OpenScan-org/OpenScan-Design/images/black-shield-config.png

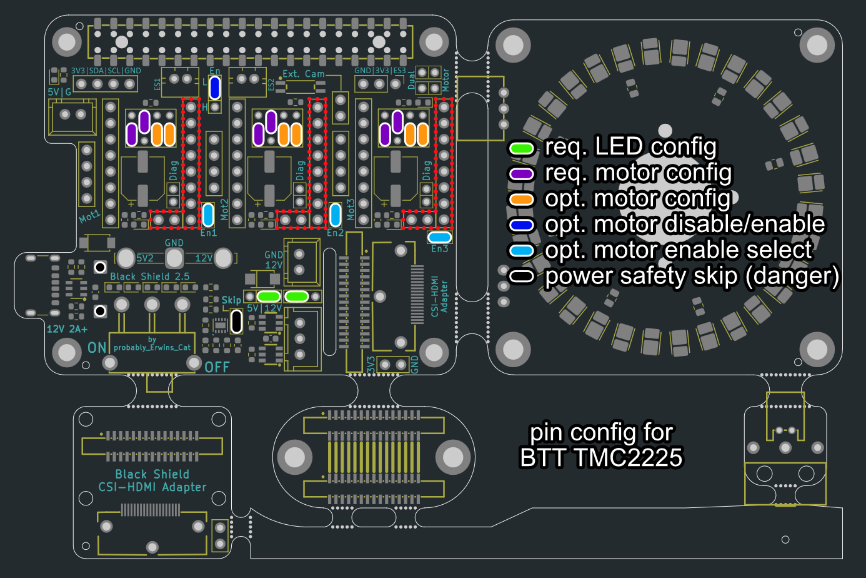
images/black-shield-config.png
