OpenScan-org/OpenScan-Design/images/cog-wheel-height-rotor.png

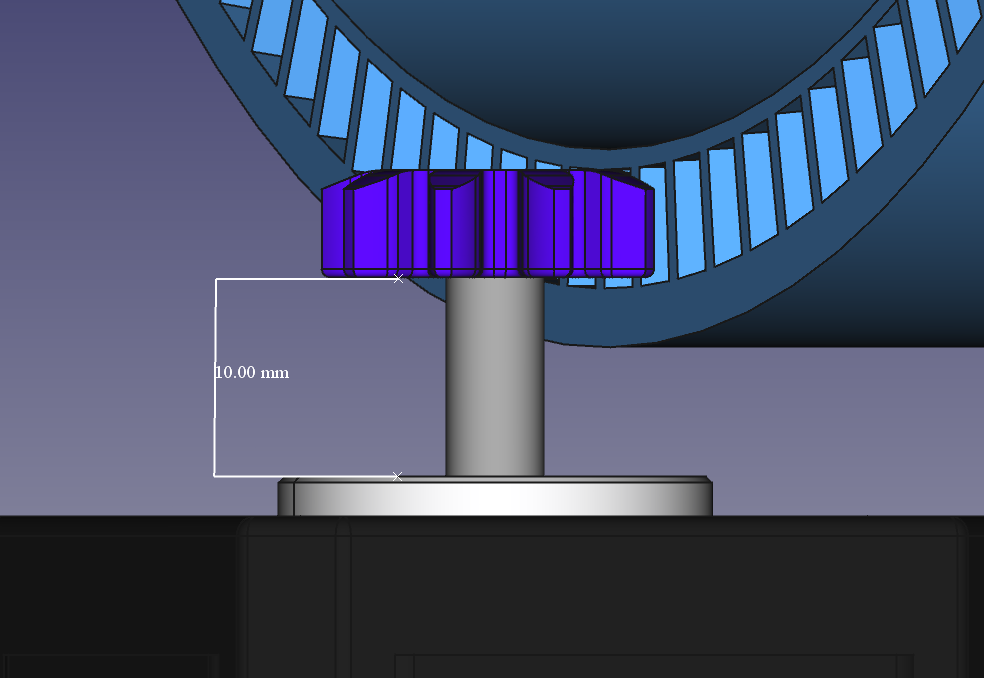
images/cog-wheel-height-rotor.png
