OpenScan-org/OpenScan-Design/images/OpenScanMiniV2Beta.jpg

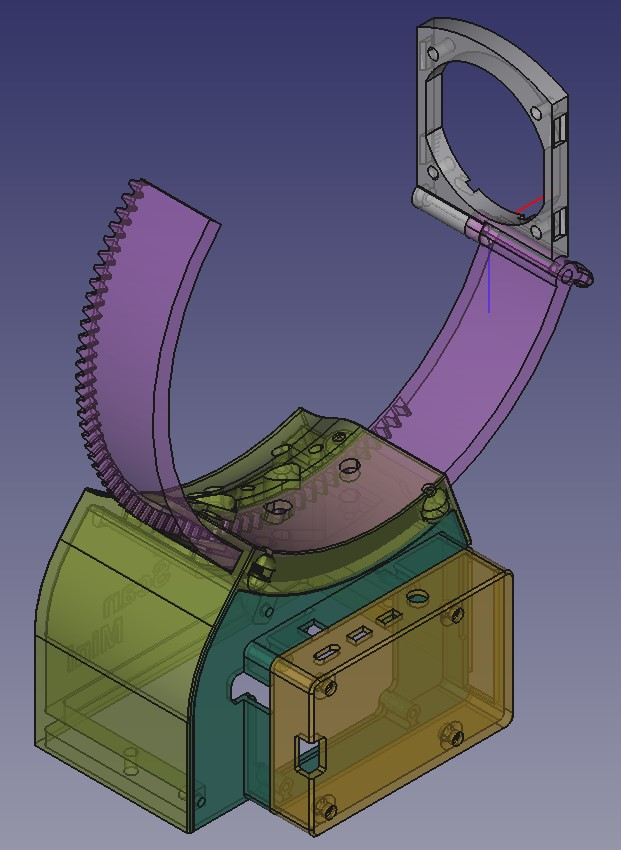
images/OpenScanMiniV2Beta.jpg
