OpenScan-org/OpenScan-Design/usermods/Turntables for D-shaped Shafts/80mm Stand for 5cm objects.3mf

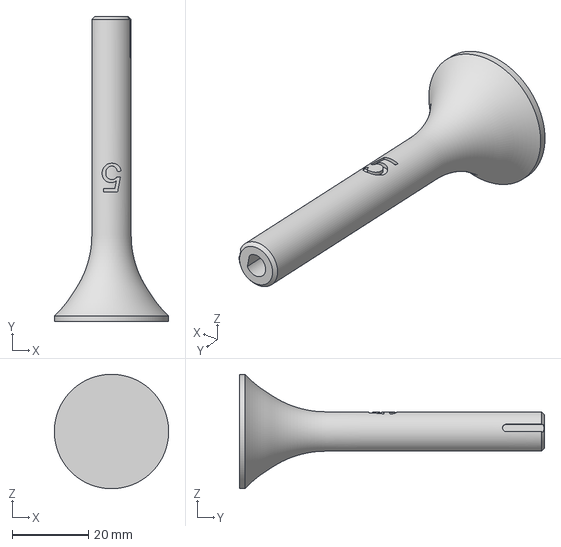
[picture p46: CAD file, 2022-10-08]
usermods/Turntables for D-shaped Shafts/80mm Stand for 5cm objects.3mf
30.0 x 80.0 x 30.0 mm
