OpenScan-org/OpenScan-Design/files/Classic/V1/Turntable_-_Adapter_small.step

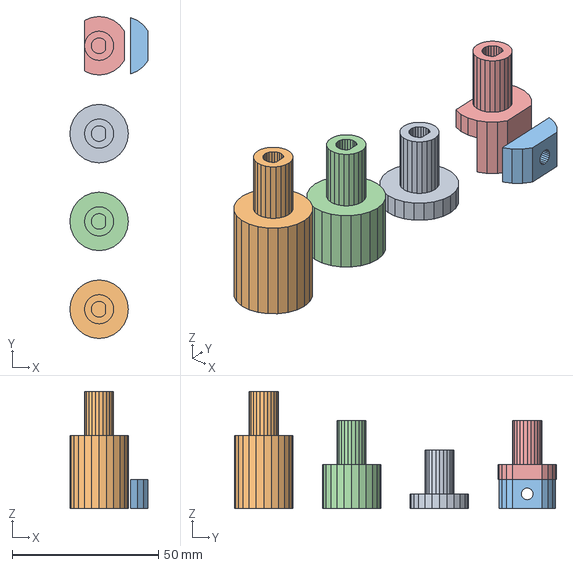
[picture p47: CAD file, 2025-07-07]
files/Classic/V1/Turntable_-_Adapter_small.step
26.8 x 110.0 x 40.0 mm
