OpenScan-org/OpenScan-Design/files/Imaging-Unit/STEP/3-IU-frame.step

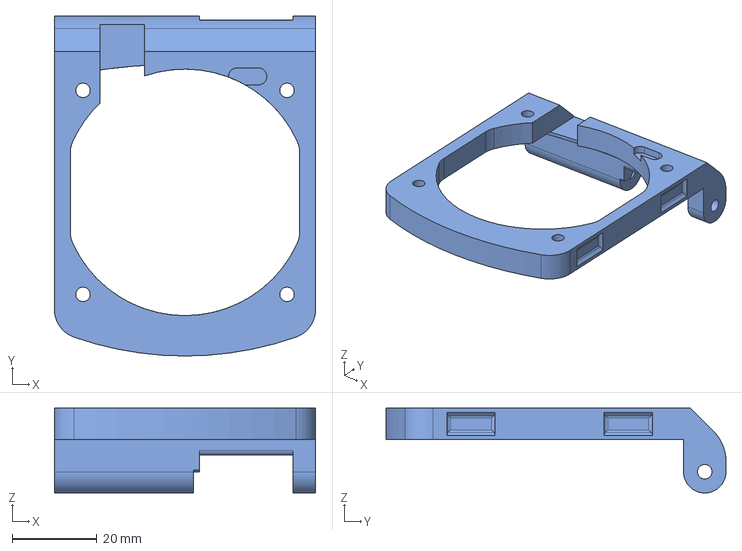
[picture p48: CAD file, 2024-12-12]
files/Imaging-Unit/STEP/3-IU-frame.step
61.5 x 80.0 x 20.0 mm
