OpenScan-org/OpenScan-Design/files/Imaging-Unit/STL/2-cam-mount-slide-in (Meshed).stl

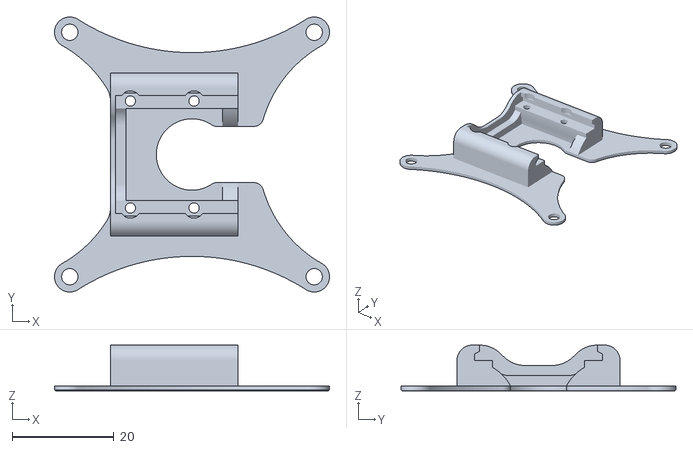
[picture p49: CAD file, 2024-12-12]
files/Imaging-Unit/STL/2-cam-mount-slide-in (Meshed).stl
54.0 x 54.0 x 9.00
