OpenScan-org/OpenScan-Design/files/Midi/V2.4/STEP/2-rotor-segmented-in-two--part-2.step

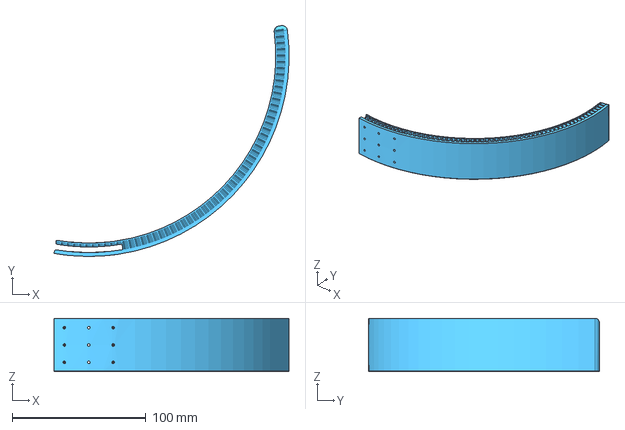
[picture p50: CAD file, 2025-06-18]
files/Midi/V2.4/STEP/2-rotor-segmented-in-two--part-2.step
176.0 x 172.9 x 40.0 mm
