OpenScan-org/OpenScan-Design/files/Midi/V2.4/STL/2-rotor-segmented-in-two--part-1 (Meshed).stl

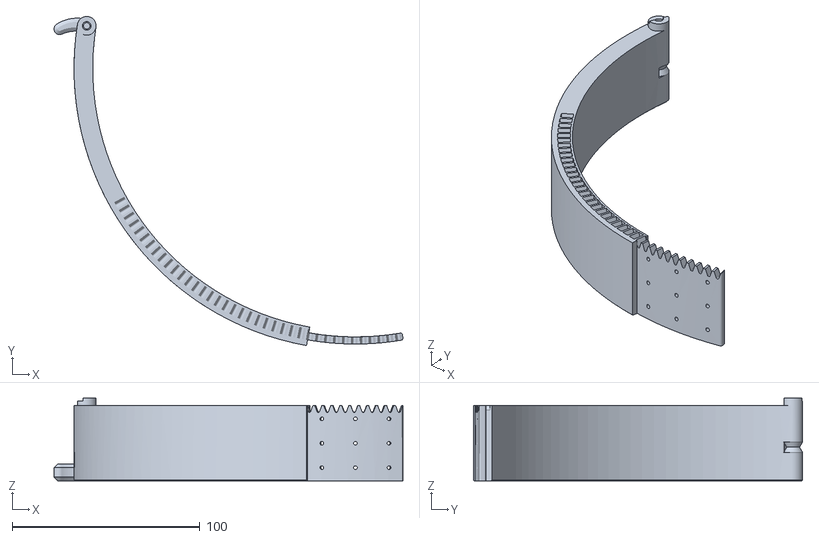
[picture p51: CAD file, 2025-06-18]
files/Midi/V2.4/STL/2-rotor-segmented-in-two--part-1 (Meshed).stl
186.0 x 175.4 x 44.0
