OpenScan-org/OpenScan-Design/files/Mini/V2.4/STEP/2-rotor-segmented-in-two--part-2.step

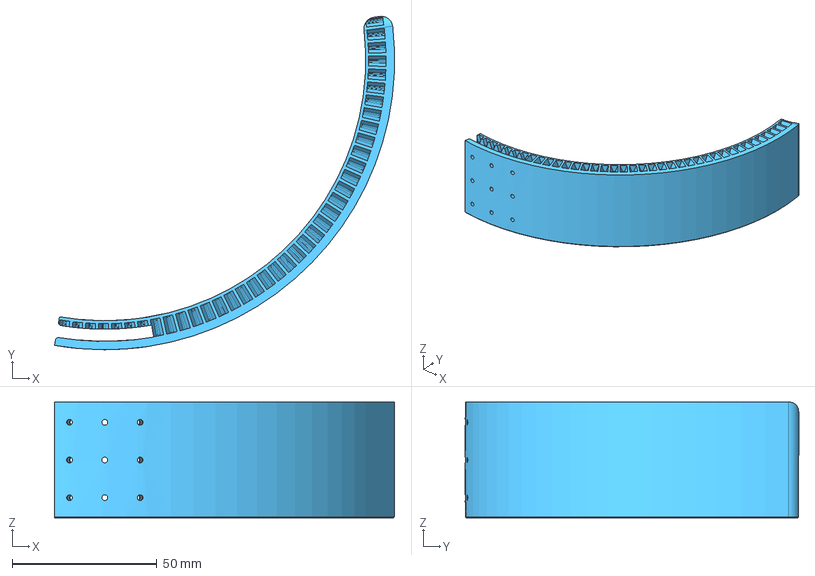
[picture p52: CAD file, 2025-06-18]
files/Mini/V2.4/STEP/2-rotor-segmented-in-two--part-2.step
117.3 x 115.1 x 40.0 mm
