OpenScan-org/OpenScan-Design/files/Mini/V2.4/STL/5-base-cover--black-shield (Meshed).stl

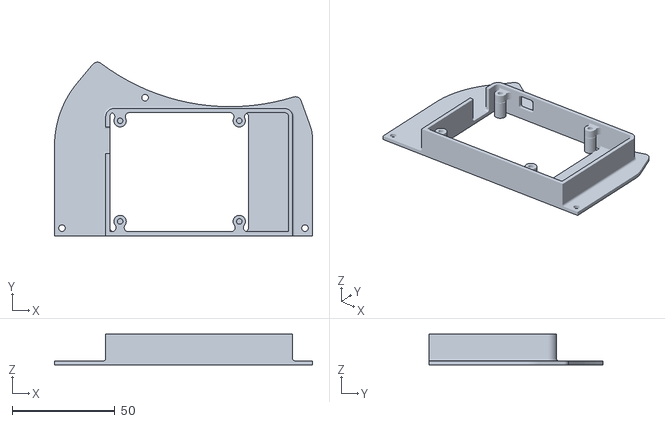
[picture p53: CAD file, 2025-06-18]
files/Mini/V2.4/STL/5-base-cover--black-shield (Meshed).stl
125.6 x 84.5 x 15.0
