OpenScan-org/OpenScan-Design/files/turntables/Midi/STEP/Turntable-90mm-object.step

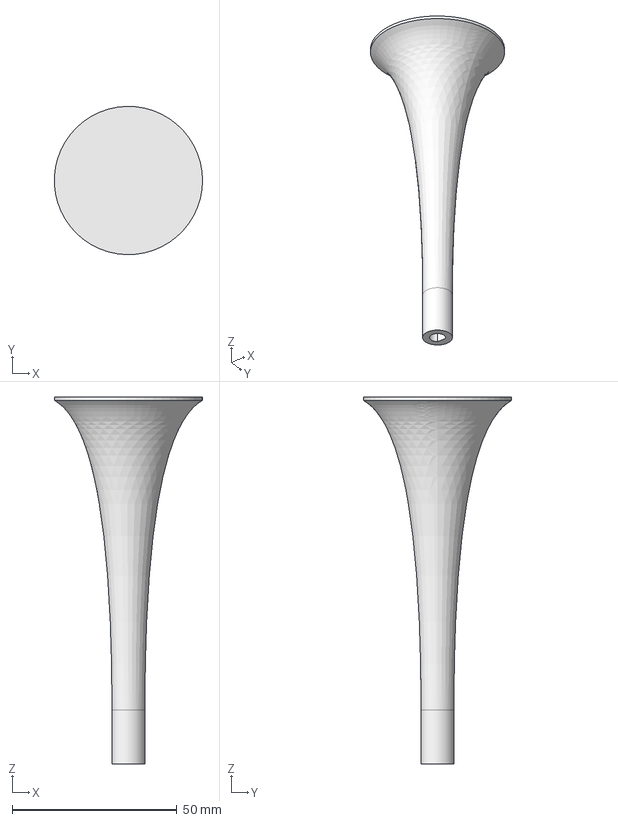
[picture p54: CAD file, 2025-03-17]
files/turntables/Midi/STEP/Turntable-90mm-object.step
45.0 x 45.0 x 111.4 mm
