OpenScan-org/OpenScan-Design/files/turntables/Mini_and_Classic/STEP/turntable-90mm-object.step

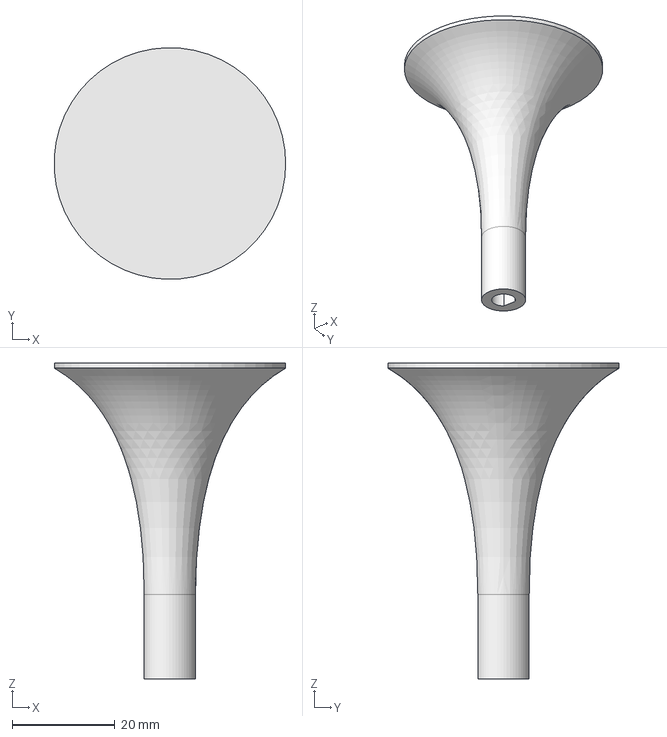
[picture p55: CAD file, 2025-03-17]
files/turntables/Mini_and_Classic/STEP/turntable-90mm-object.step
45.0 x 45.0 x 61.4 mm
