OpenScan-org/OpenScan-Design/OS-Midi/spherical-dome.stl

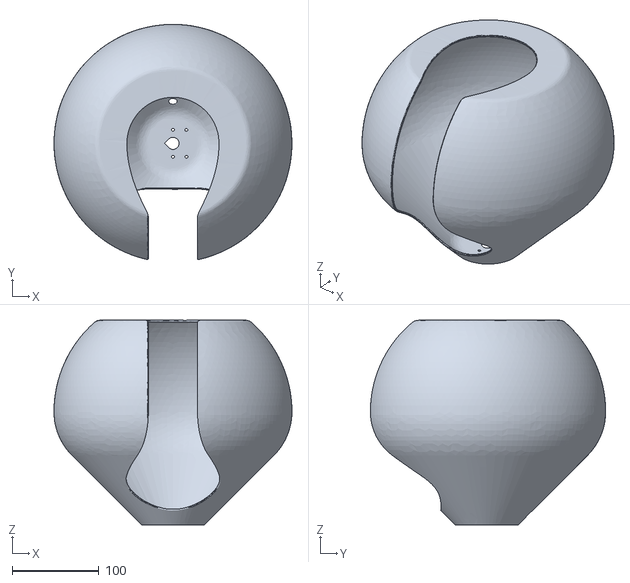
[picture p56: CAD file, 2023-12-23]
OS-Midi/spherical-dome.stl
273.9 x 270.7 x 235.4
