OpenScan-org/OpenScan-Design/OS-Mini/V2/optional-spherical-dome.stl

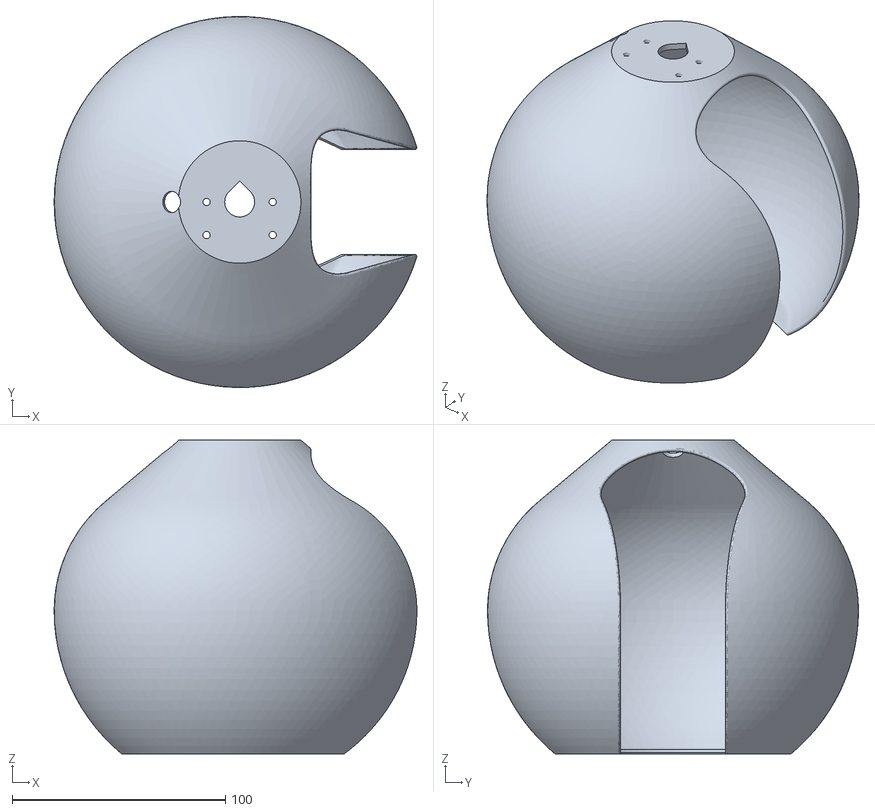
[picture p57: CAD file, 2024-03-03]
OS-Mini/V2/optional-spherical-dome.stl
170.1 x 174.0 x 147.1
