OpenScan-org/OpenScan-Design/usermods/Turntables for D-shaped Shafts/90mm Stand for 3cm objects.3mf

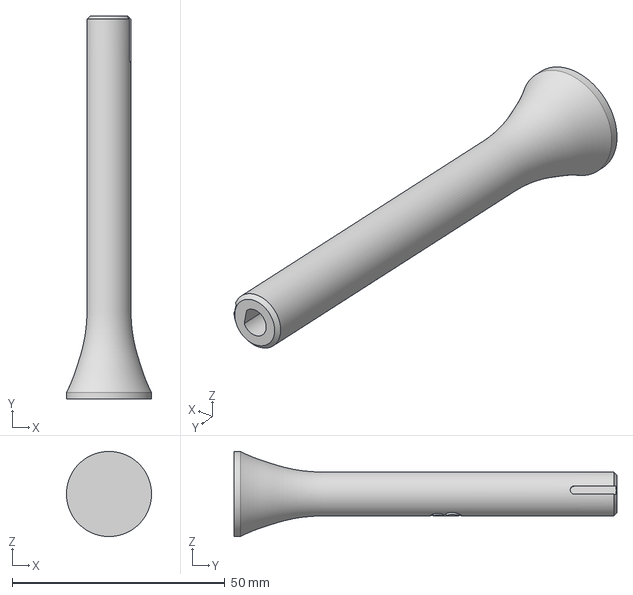
[picture p58: CAD file, 2022-10-08]
usermods/Turntables for D-shaped Shafts/90mm Stand for 3cm objects.3mf
20.0 x 90.0 x 20.0 mm
