OpenScan-org/OpenScan-Design/files/Classic/V1/Turntable_-_Adapter_large.step

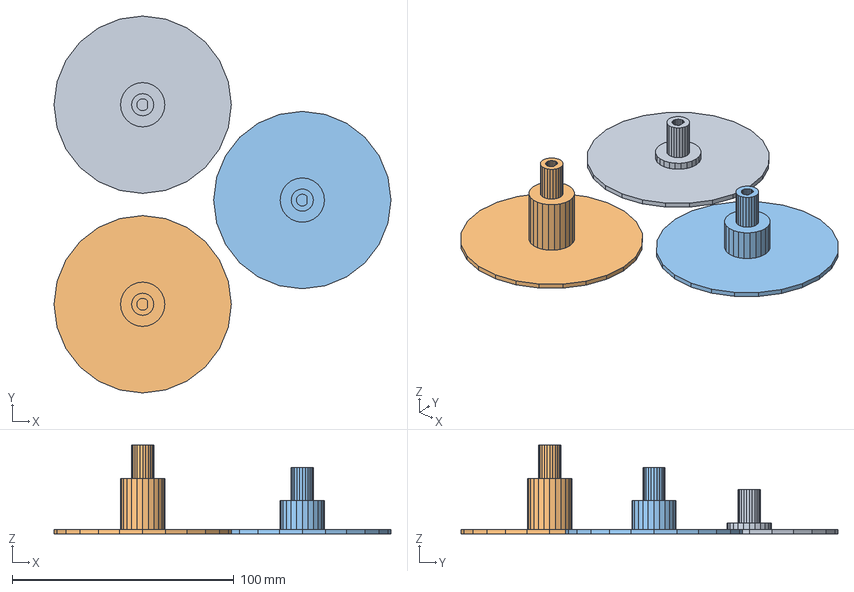
[picture p59: CAD file, 2025-07-07]
files/Classic/V1/Turntable_-_Adapter_large.step
152.0 x 170.0 x 40.0 mm
