OpenScan-org/OpenScan-Design/files/Imaging-Unit/STEP/4-camera-polarizer-opaque.step

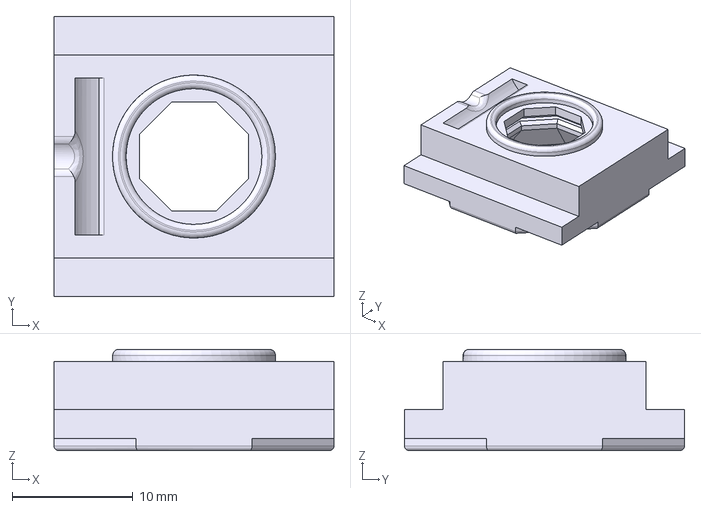
[picture p60: CAD file, 2024-12-12]
files/Imaging-Unit/STEP/4-camera-polarizer-opaque.step
23.2 x 23.2 x 8.40 mm
