OpenScan-org/OpenScan-Design/files/Imaging-Unit/STL/3-IU-frame (Meshed).stl

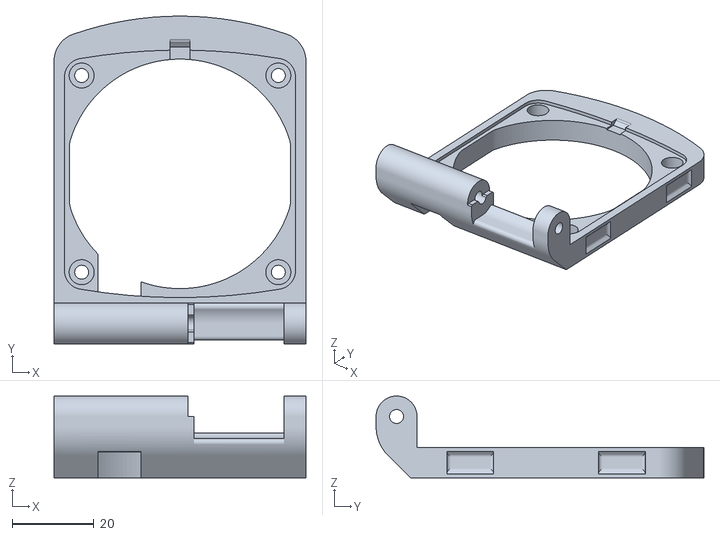
[picture p61: CAD file, 2024-12-12]
files/Imaging-Unit/STL/3-IU-frame (Meshed).stl
61.5 x 80.0 x 20.0
