OpenScan-org/OpenScan-Design/files/Midi/V2.4/STEP/5-base-cover--black-shield.step

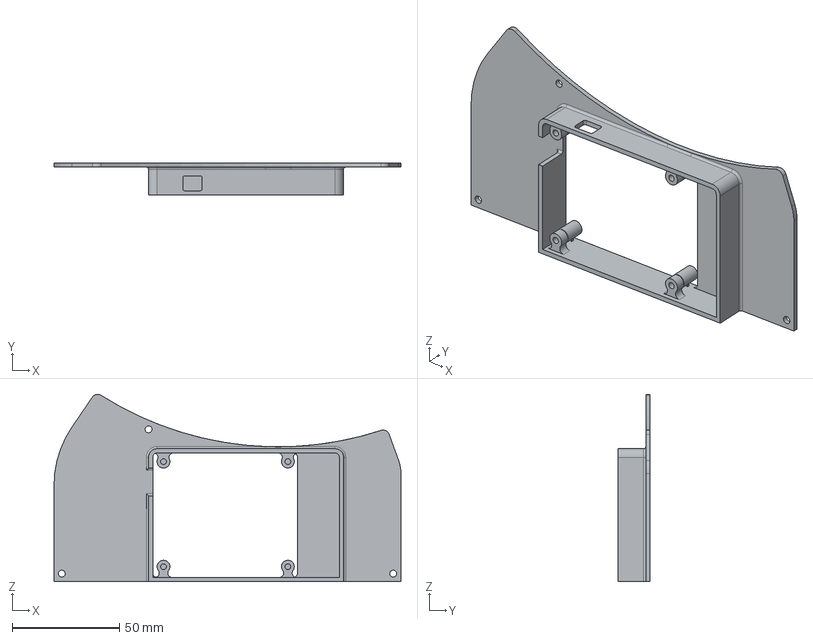
[picture p62: CAD file, 2025-06-18]
files/Midi/V2.4/STEP/5-base-cover--black-shield.step
161.8 x 15.0 x 87.4 mm
