OpenScan-org/OpenScan-Design/files/Midi/V2.4/STL/2-rotor-segmented-in-three--part-3 (Meshed).stl

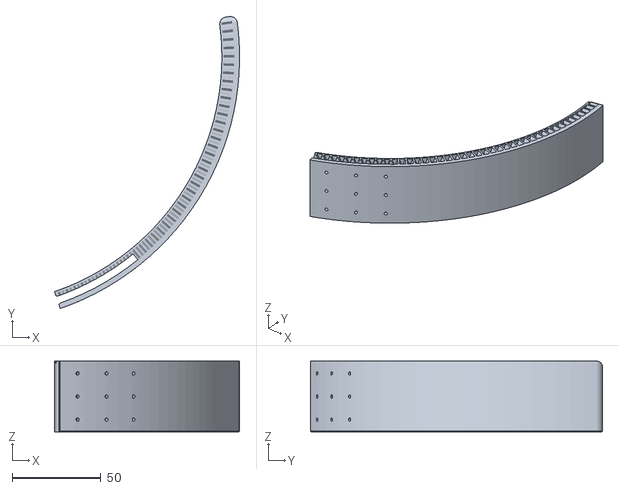
[picture p63: CAD file, 2025-06-18]
files/Midi/V2.4/STL/2-rotor-segmented-in-three--part-3 (Meshed).stl
104.4 x 164.7 x 40.0
