OpenScan-org/OpenScan-Design/files/Mini/V2.4/STEP/optional-paper-dome.step

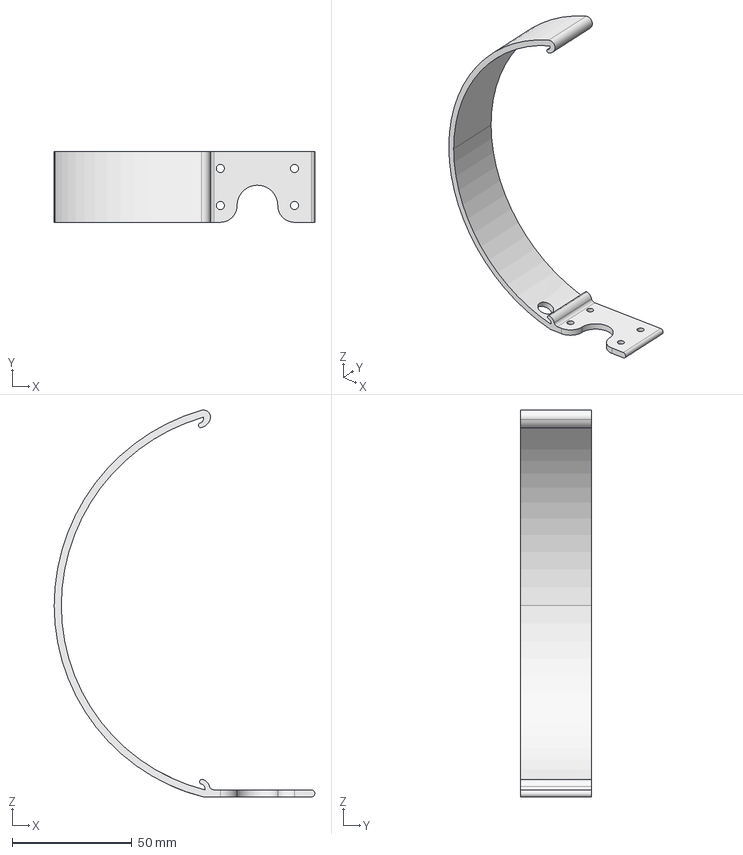
[picture p64: CAD file, 2025-06-18]
files/Mini/V2.4/STEP/optional-paper-dome.step
109.0 x 29.5 x 161.8 mm
