OpenScan-org/OpenScan-Design/files/Mini/V2.4/STL/2-rotor-segmented-in-two--part-1 (Meshed).stl

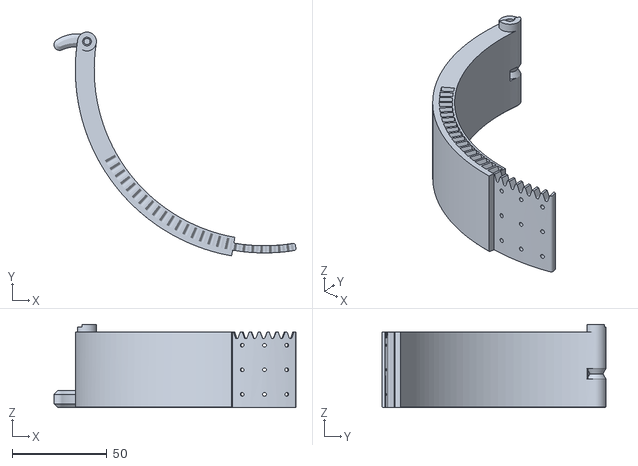
[picture p65: CAD file, 2025-06-18]
files/Mini/V2.4/STL/2-rotor-segmented-in-two--part-1 (Meshed).stl
127.9 x 118.3 x 44.0
