OpenScan-org/OpenScan-Design/files/turntables/Midi/STEP/Turntable-150mm-object.step

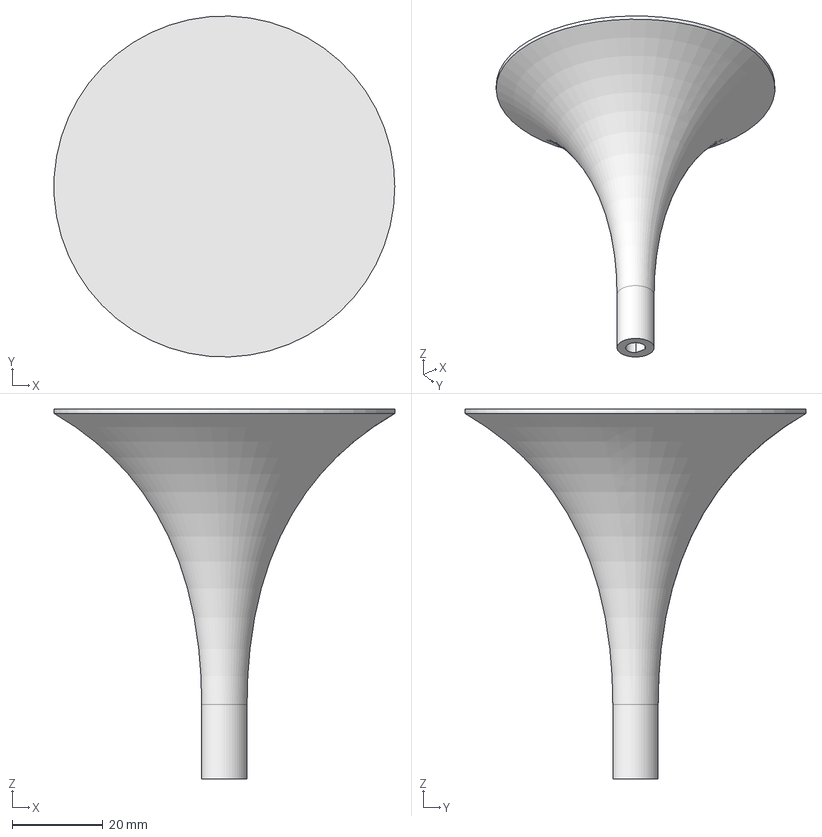
[picture p66: CAD file, 2025-03-17]
files/turntables/Midi/STEP/Turntable-150mm-object.step
74.9 x 75.0 x 81.4 mm
