OpenScan-org/OpenScan-Design/files/turntables/Mini_and_Classic/STEP/turntable-30mm-object.step

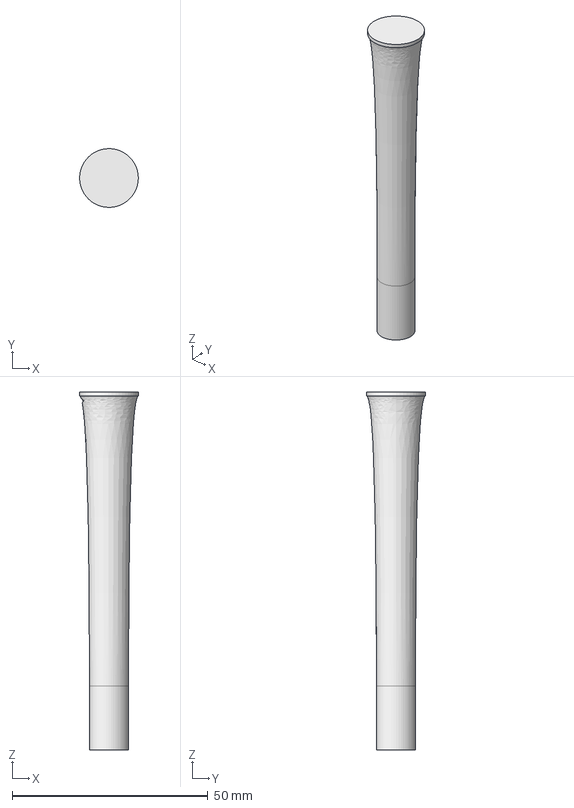
[picture p67: CAD file, 2025-03-17]
files/turntables/Mini_and_Classic/STEP/turntable-30mm-object.step
15.0 x 15.0 x 91.4 mm
