OpenScan-org/OpenScan-Design/OS-Mini/V2/spherical-dome.stl

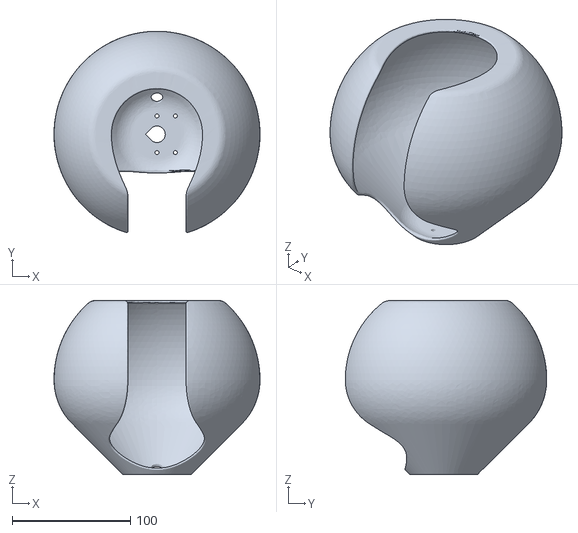
[picture p68: CAD file, 2023-12-23]
OS-Mini/V2/spherical-dome.stl
174.0 x 170.0 x 147.2
