OpenScan-org/OpenScan-Design/usermods/Turntables for D-shaped Shafts/70mm Stand for 7cm objects.3mf

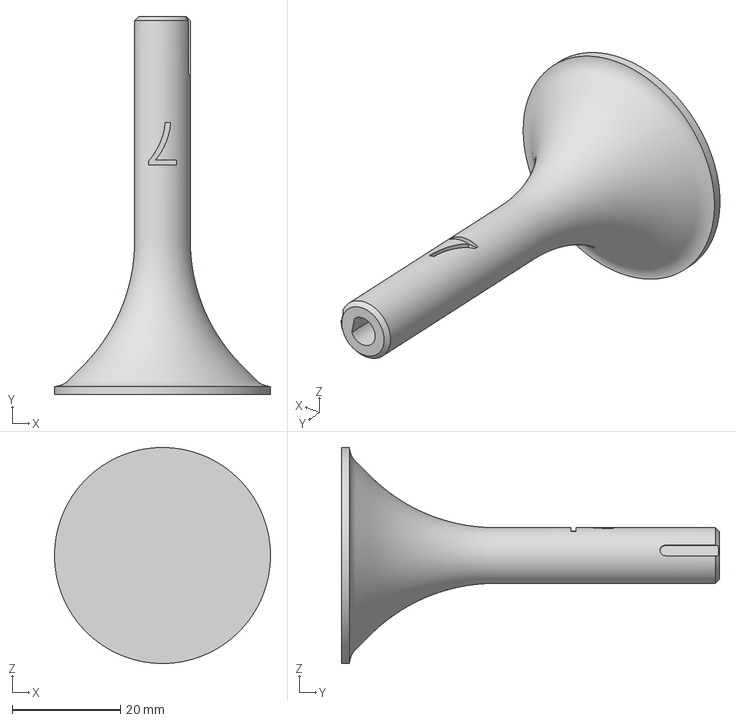
[picture p69: CAD file, 2022-10-08]
usermods/Turntables for D-shaped Shafts/70mm Stand for 7cm objects.3mf
40.0 x 70.0 x 40.0 mm
