OpenScan-org/OpenScan-Design/files/Classic/V1/Turntable_Base_Large_Version_35cm_split_version_by_Paul.step

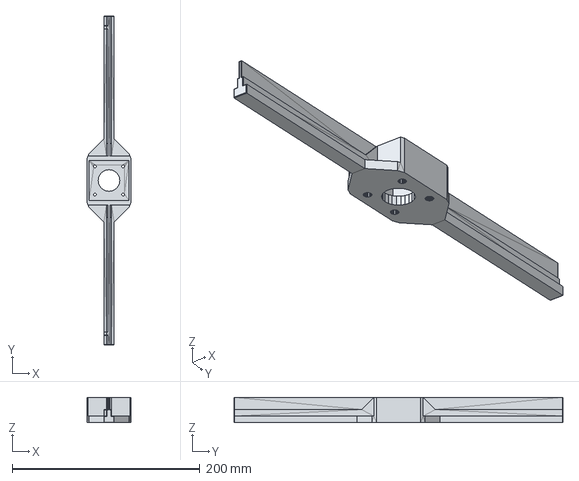
[picture p70: CAD file, 2025-07-07]
files/Classic/V1/Turntable_Base_Large_Version_35cm_split_version_by_Paul.step
47.0 x 350.0 x 27.0 mm
