OpenScan-org/OpenScan-Design/files/Imaging-Unit/STEP/1-IU-Cover.step

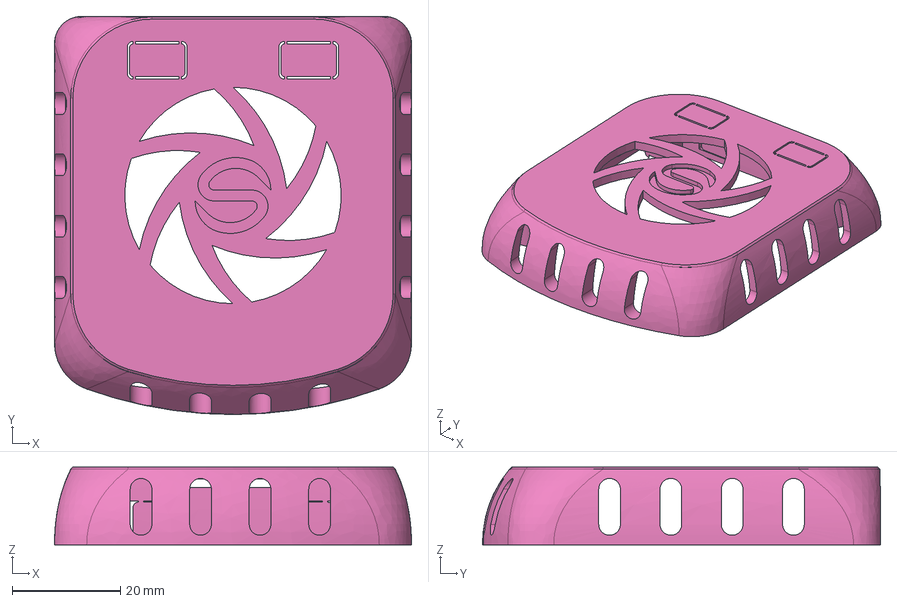
[picture p71: CAD file, 2024-12-12]
files/Imaging-Unit/STEP/1-IU-Cover.step
66.0 x 73.6 x 14.4 mm
