OpenScan-org/OpenScan-Design/files/Midi/V2.4/STEP/optional-paper-dome.step

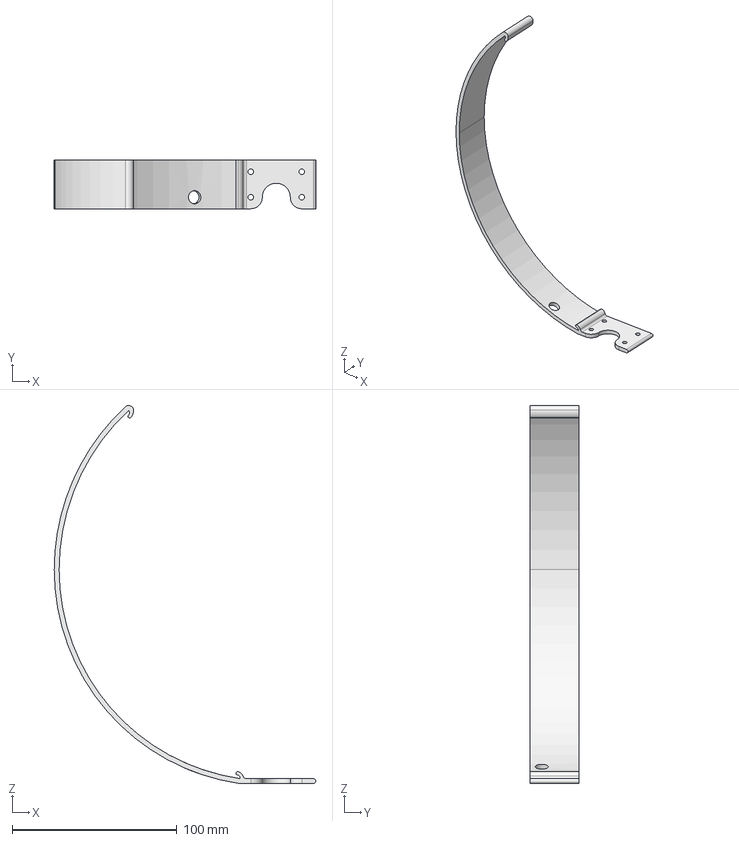
[picture p72: CAD file, 2025-06-18]
files/Midi/V2.4/STEP/optional-paper-dome.step
159.0 x 29.5 x 229.8 mm
