OpenScan-org/OpenScan-Design/files/Mini/V2.4/STEP/2-rotor-segmented-in-three--part-3.step

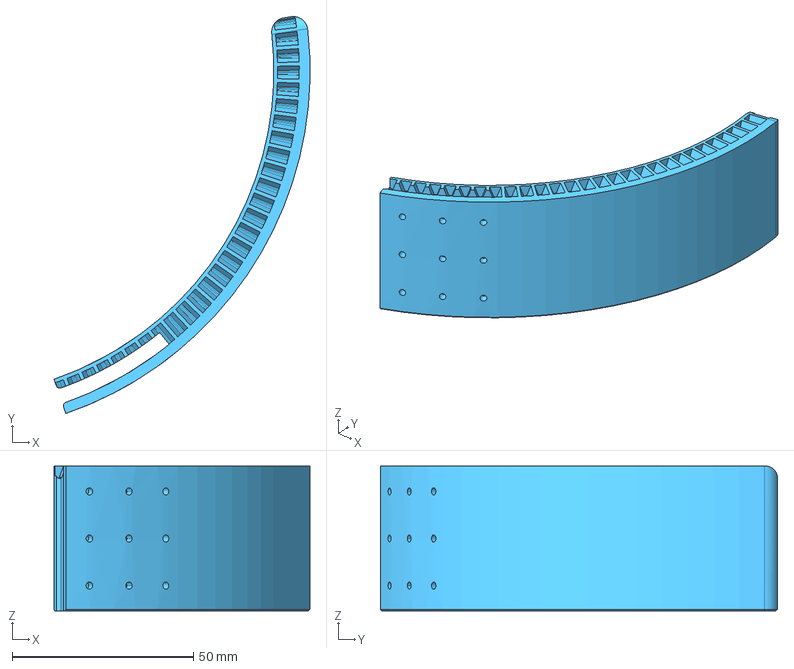
[picture p73: CAD file, 2025-06-18]
files/Mini/V2.4/STEP/2-rotor-segmented-in-three--part-3.step
70.7 x 109.6 x 40.0 mm
