OpenScan-org/OpenScan-Design/files/turntables/Midi/STEP/Turntable-30mm-object.step

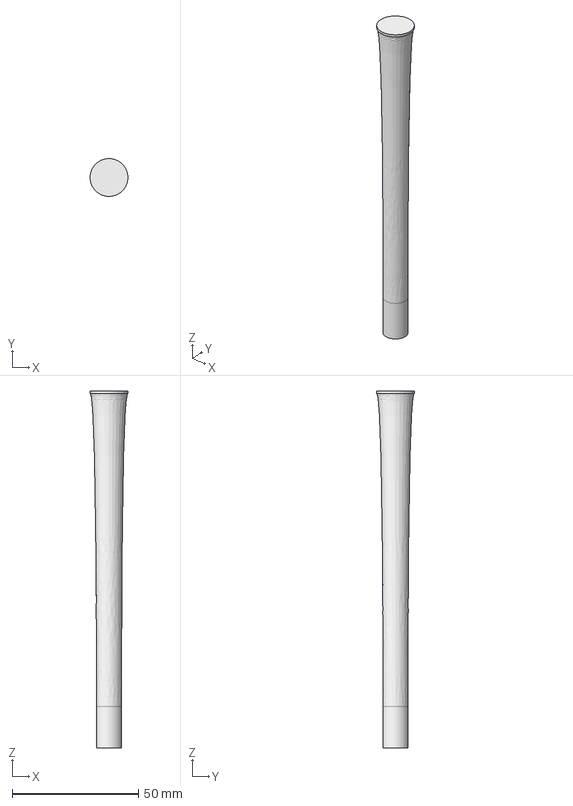
[picture p74: CAD file, 2025-03-17]
files/turntables/Midi/STEP/Turntable-30mm-object.step
15.0 x 15.0 x 141.4 mm
