OpenScan-org/OpenScan-Design/files/turntables/Mini_and_Classic/STEP/turntable-80mm-object.step

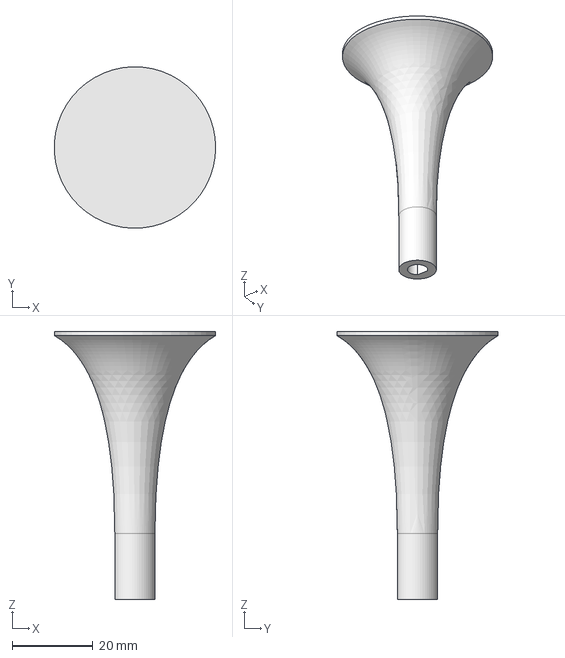
[picture p75: CAD file, 2025-03-17]
files/turntables/Mini_and_Classic/STEP/turntable-80mm-object.step
40.0 x 40.0 x 66.4 mm
