OpenScan-org/OpenScan-Design/usermods/Enhanced Diffuser (Classic)/Camera Shade.stl

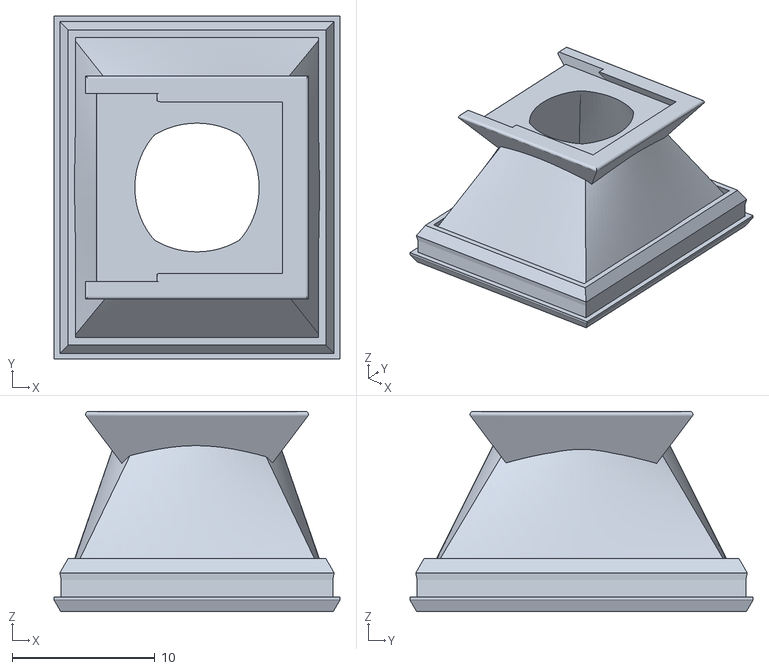
[picture p76: CAD file, 2025-03-26]
usermods/Enhanced Diffuser (Classic)/Camera Shade.stl
20.0 x 24.0 x 14.0
