OpenScan-org/OpenScan-Design/usermods/Turntables for D-shaped Shafts/55mm Stand for 10cm objects.3mf

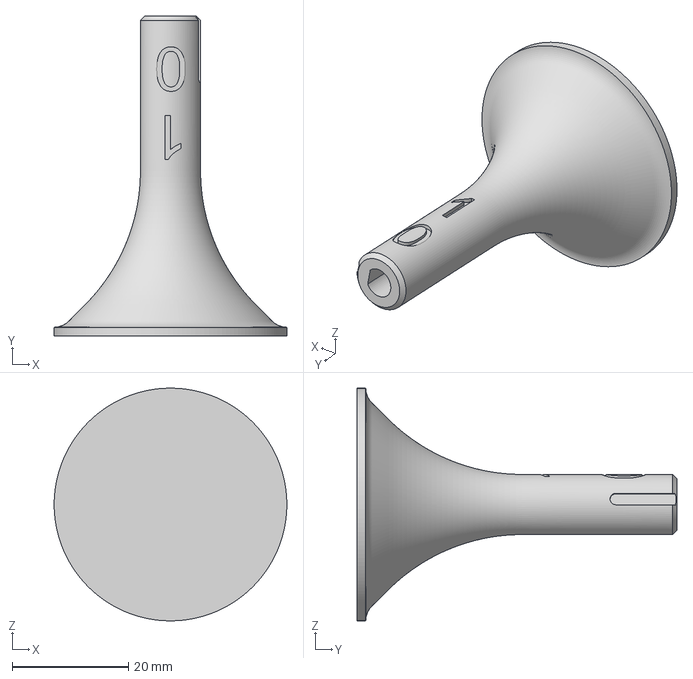
[picture p77: CAD file, 2022-10-08]
usermods/Turntables for D-shaped Shafts/55mm Stand for 10cm objects.3mf
40.0 x 55.0 x 40.0 mm
