OpenScan-org/OpenScan-Design/files/Classic/V1/Turntable_Base_large_version_35cm.step

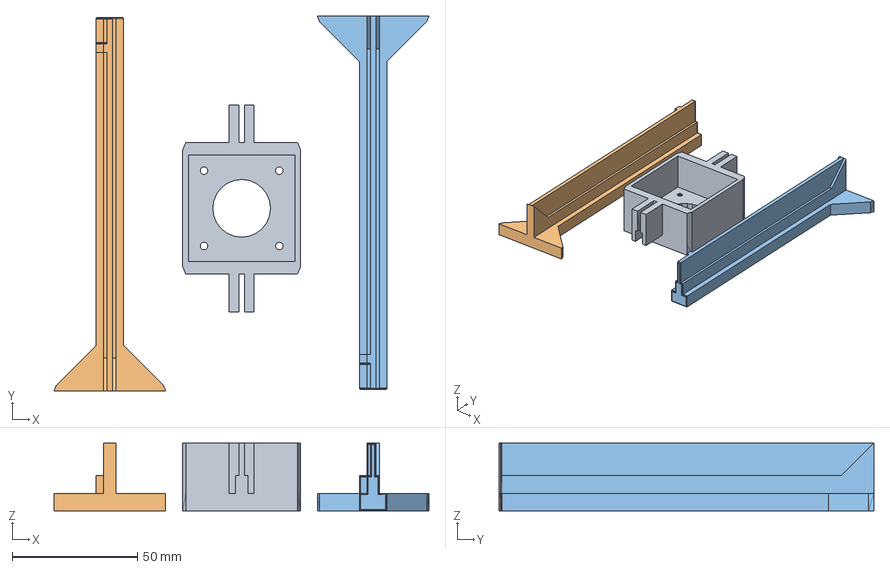
[picture p78: CAD file, 2025-07-07]
files/Classic/V1/Turntable_Base_large_version_35cm.step
149.4 x 149.3 x 27.0 mm
