OpenScan-org/OpenScan-Design/files/Imaging-Unit/STEP/2-cam-mount-slide-in.step

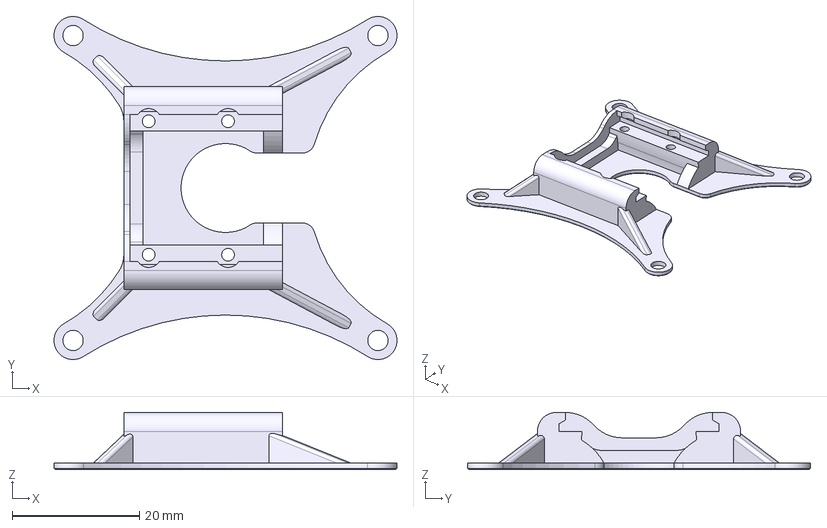
[picture p79: CAD file, 2024-12-12]
files/Imaging-Unit/STEP/2-cam-mount-slide-in.step
54.0 x 54.0 x 9.00 mm
