OpenScan-org/OpenScan-Design/files/Imaging-Unit/STL/optional-polarizer-Cutting-Guide (Meshed).stl

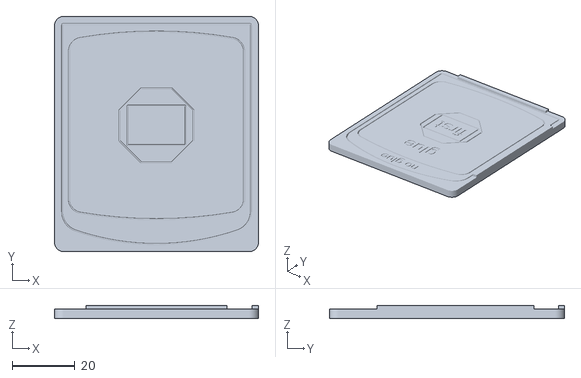
[picture p80: CAD file, 2024-12-12]
files/Imaging-Unit/STL/optional-polarizer-Cutting-Guide (Meshed).stl
65.0 x 75.0 x 4.00
