OpenScan-org/OpenScan-Design/files/Midi/V2.4/STEP/2-rotor-segmented-in-three--part-2.step

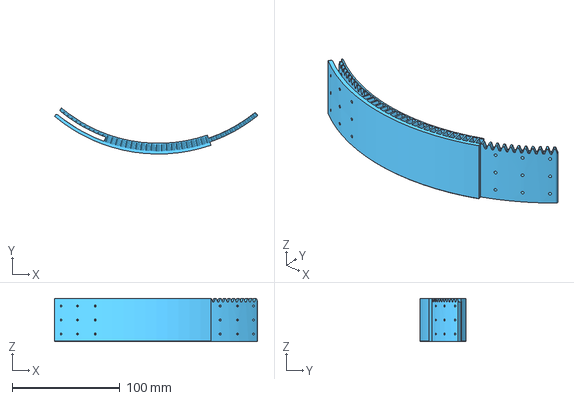
[picture p81: CAD file, 2025-06-18]
files/Midi/V2.4/STEP/2-rotor-segmented-in-three--part-2.step
188.5 x 42.7 x 40.0 mm
