OpenScan-org/OpenScan-Design/files/Mini/V2.4/STEP/2-rotor-segmented-in-three--part-2.step

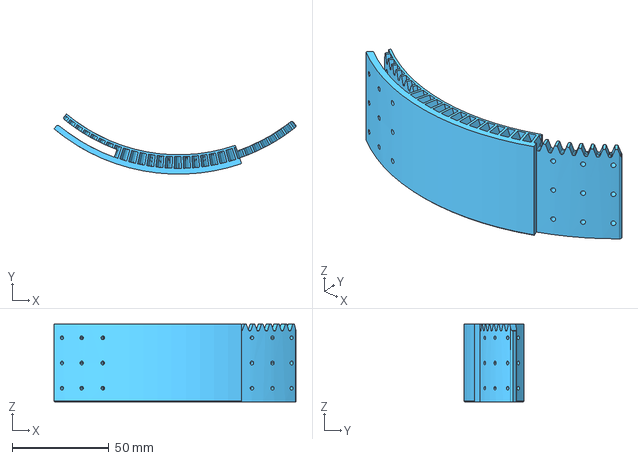
[picture p82: CAD file, 2025-06-18]
files/Mini/V2.4/STEP/2-rotor-segmented-in-three--part-2.step
124.9 x 31.0 x 40.0 mm
