OpenScan-org/OpenScan-Design/files/turntables/Midi/STEP/Turntable-70mm-object.step

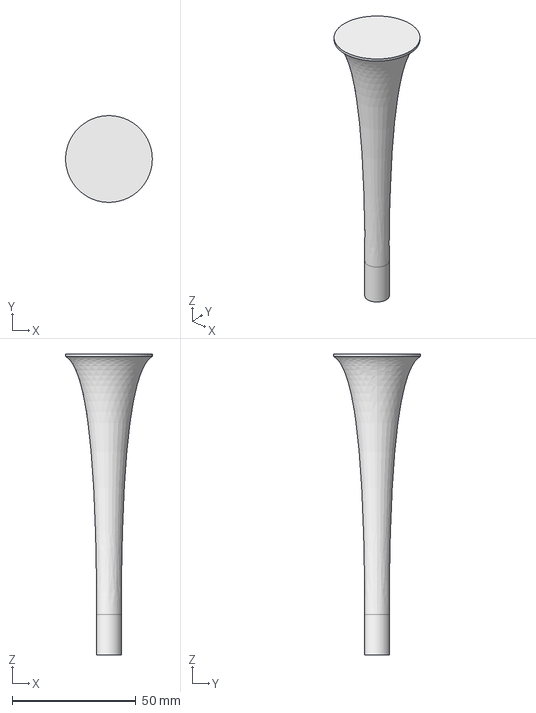
[picture p83: CAD file, 2025-03-17]
files/turntables/Midi/STEP/Turntable-70mm-object.step
35.0 x 35.0 x 121.4 mm
