OpenScan-org/OpenScan-Design/files/turntables/Mini_and_Classic/STEP/turntable-70mm-object.step

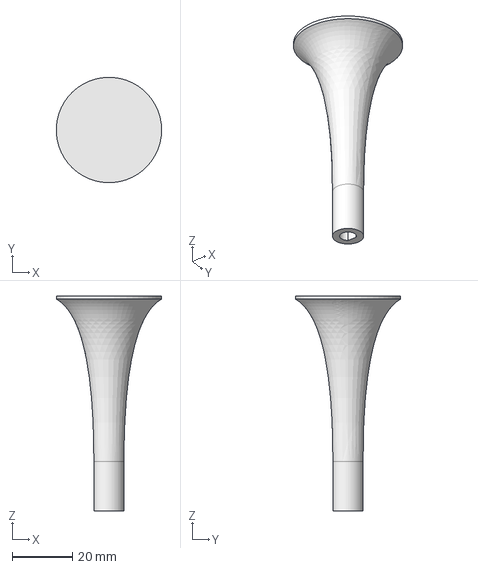
[picture p84: CAD file, 2025-03-17]
files/turntables/Mini_and_Classic/STEP/turntable-70mm-object.step
35.0 x 35.0 x 71.4 mm
