OpenScan-org/OpenScan-Design/usermods/Enhanced Diffuser (Classic)/Polariser Templates.stl

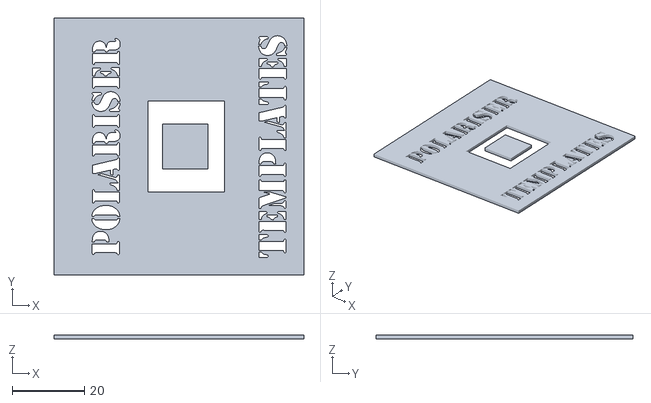
[picture p85: CAD file, 2025-03-26]
usermods/Enhanced Diffuser (Classic)/Polariser Templates.stl
69.0 x 71.0 x 1.20
