OpenScan-org/OpenScan-Design/files/Imaging-Unit/STL/6-Polarizer-Hood (Meshed).stl

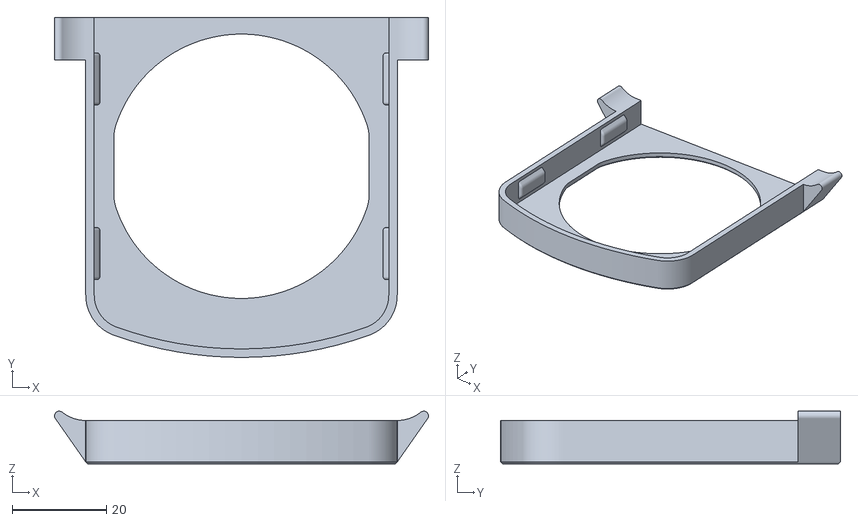
[picture p86: CAD file, 2024-12-12]
files/Imaging-Unit/STL/6-Polarizer-Hood (Meshed).stl
79.2 x 72.0 x 11.2
