OpenScan-org/OpenScan-Design/files/turntables/Midi/STEP/Turntable-130mm-object.step

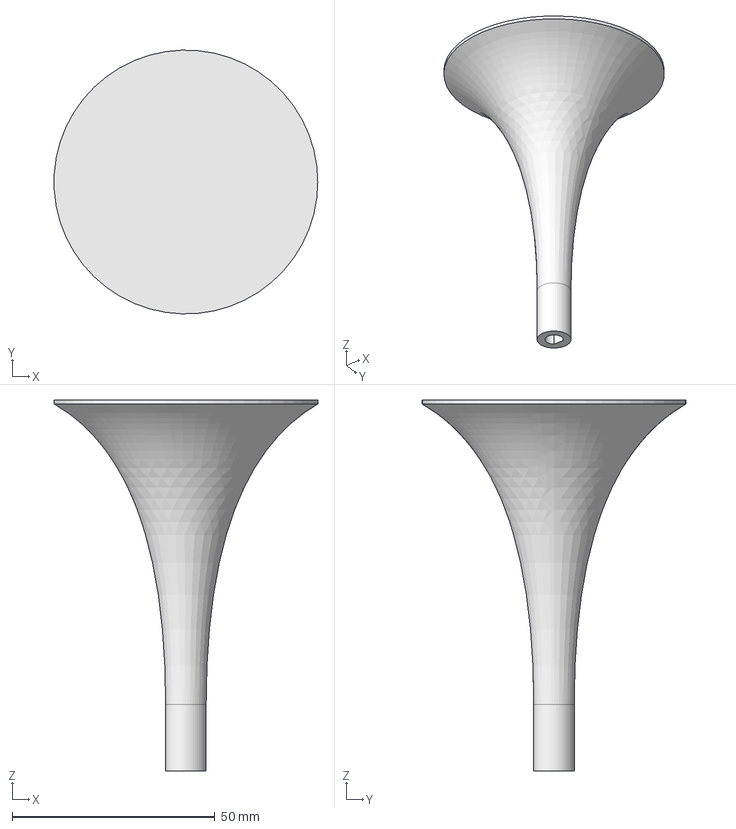
[picture p87: CAD file, 2025-03-17]
files/turntables/Midi/STEP/Turntable-130mm-object.step
64.9 x 65.0 x 91.4 mm
