OpenScan-org/OpenScan-Design/files/turntables/Mini_and_Classic/STEP/turntable-50mm-object.step

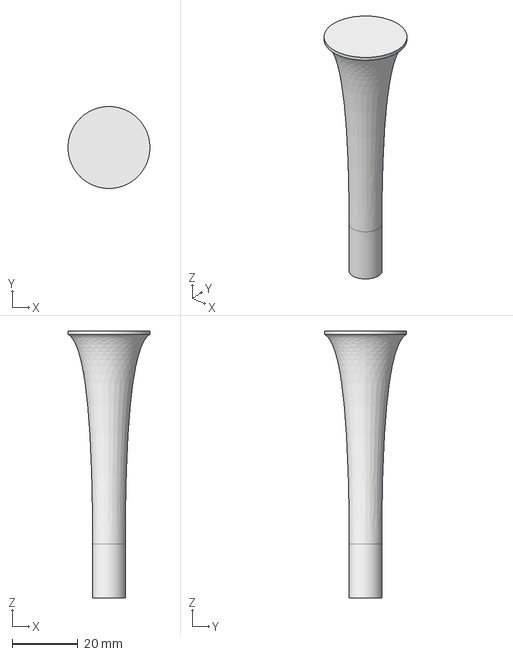
[picture p88: CAD file, 2025-03-17]
files/turntables/Mini_and_Classic/STEP/turntable-50mm-object.step
25.0 x 25.0 x 81.4 mm
