OpenScan-org/OpenScan-Design/usermods/Enhanced Diffuser (Classic)/Large Polariser Clip.stl

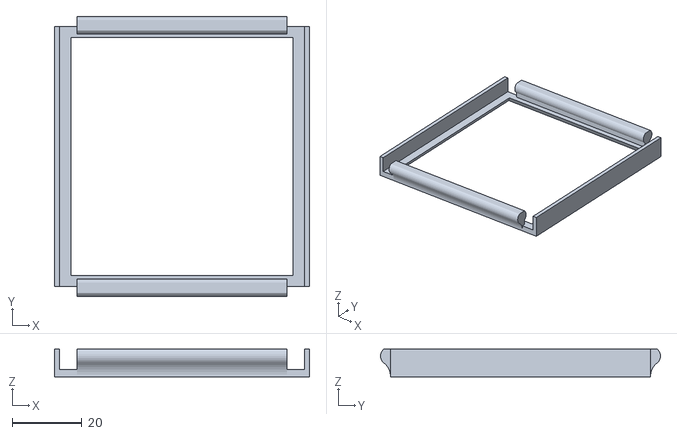
[picture p89: CAD file, 2025-03-26]
usermods/Enhanced Diffuser (Classic)/Large Polariser Clip.stl
73.1 x 80.3 x 8.00
