OpenScan-org/OpenScan-Design/files/Classic/V1/Rotary_Arm_-_2x.step

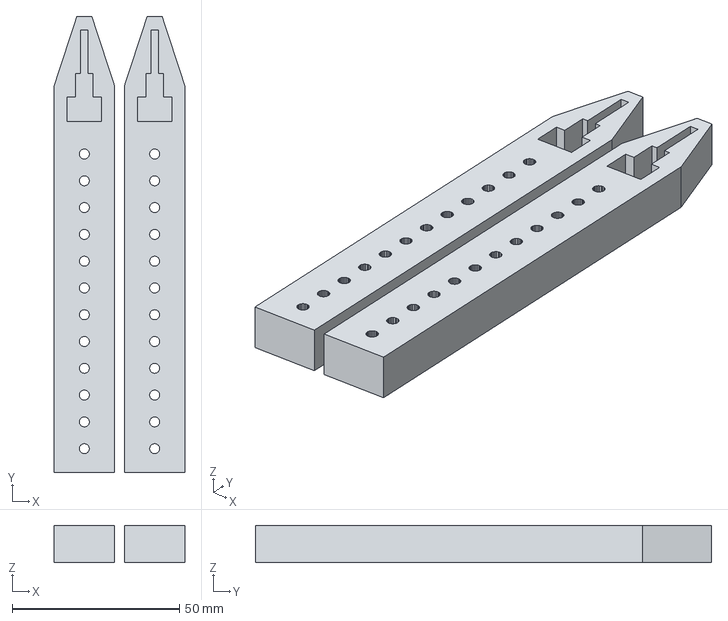
[picture p90: CAD file, 2025-07-07]
files/Classic/V1/Rotary_Arm_-_2x.step
39.0 x 136.2 x 11.2 mm
