OpenScan-org/OpenScan-Design/files/Imaging-Unit/STEP/5-Light-Polarizer-clear-or-natural.step

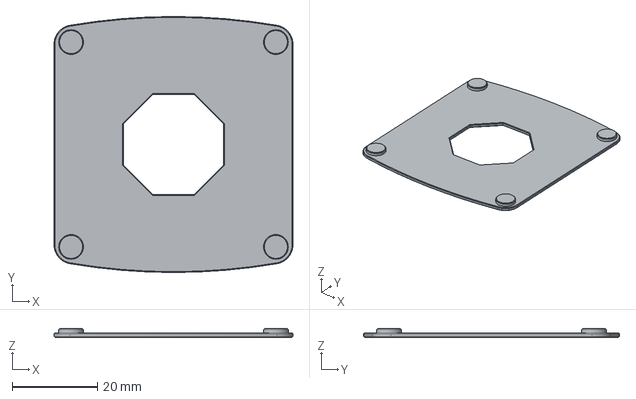
[picture p91: CAD file, 2024-12-12]
files/Imaging-Unit/STEP/5-Light-Polarizer-clear-or-natural.step
56.0 x 60.0 x 2.00 mm
