OpenScan-org/OpenScan-Design/files/Midi/V2.4/STEP/2-rotor-unibody.step

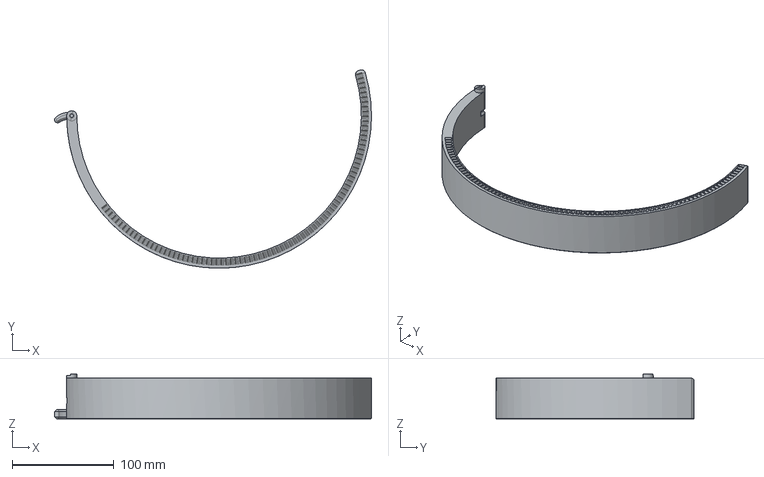
[picture p92: CAD file, 2025-06-18]
files/Midi/V2.4/STEP/2-rotor-unibody.step
312.0 x 195.3 x 44.0 mm
