OpenScan-org/OpenScan-Design/files/Midi/V2.4/STL/2-rotor-segmented-in-three--part-1 (Meshed).stl

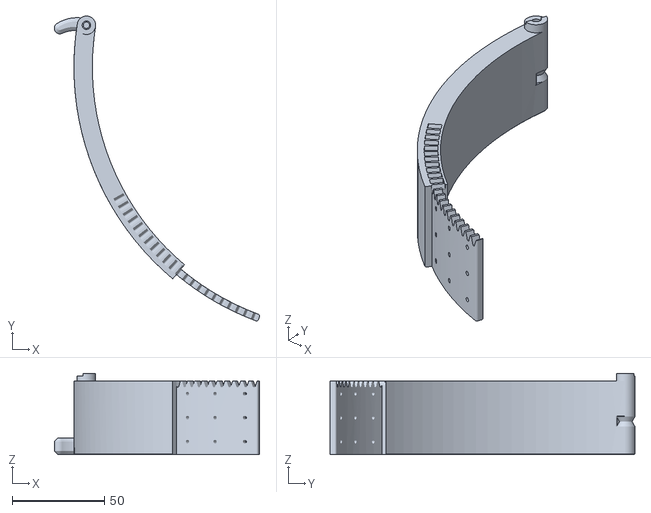
[picture p93: CAD file, 2025-06-18]
files/Midi/V2.4/STL/2-rotor-segmented-in-three--part-1 (Meshed).stl
111.4 x 165.4 x 44.0
