OpenScan-org/OpenScan-Design/files/turntables/Midi/STEP/Turntable-50mm-object.step

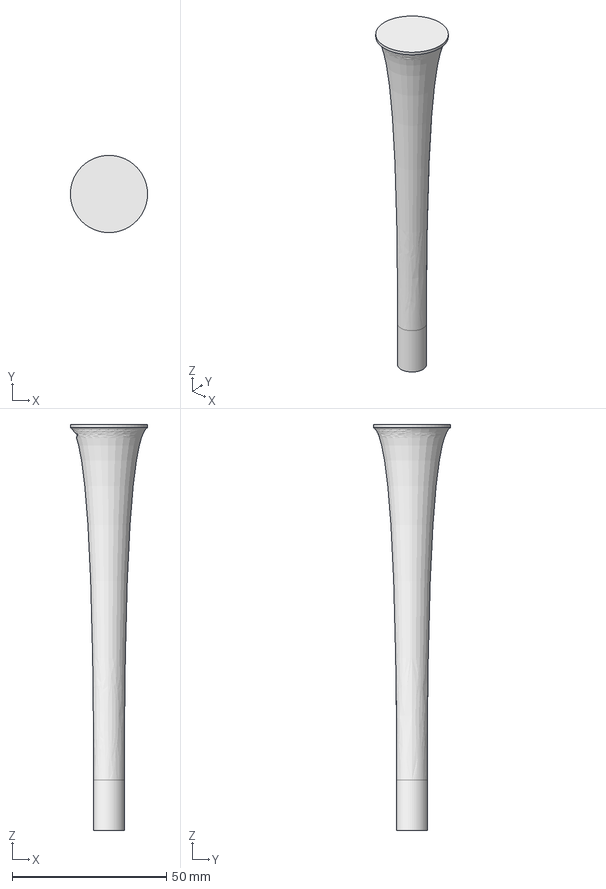
[picture p94: CAD file, 2025-03-17]
files/turntables/Midi/STEP/Turntable-50mm-object.step
25.0 x 25.0 x 131.4 mm
