OpenScan-org/OpenScan-Design/files/turntables/Mini_and_Classic/STEP/turntable-40mm-object.step

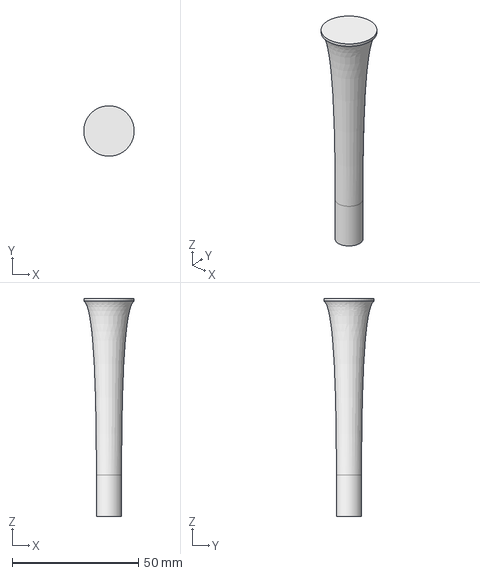
[picture p95: CAD file, 2025-03-17]
files/turntables/Mini_and_Classic/STEP/turntable-40mm-object.step
20.0 x 20.0 x 86.4 mm
