OpenScan-org/OpenScan-Design/files/Classic/V1/stand2.step

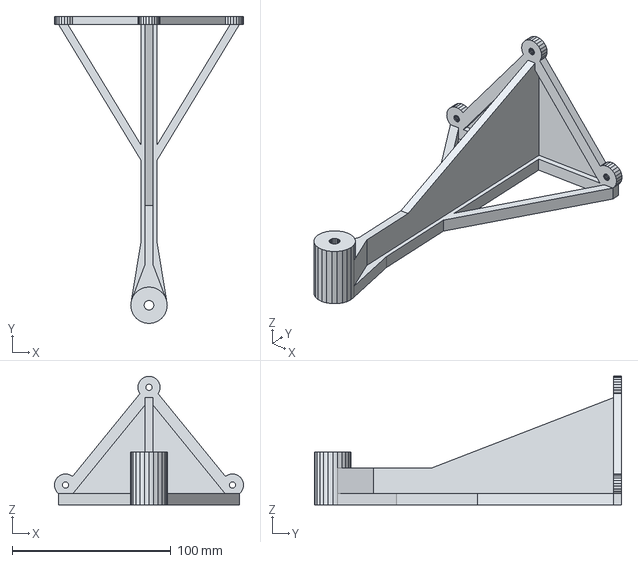
[picture p96: CAD file, 2025-07-07]
files/Classic/V1/stand2.step
119.0 x 193.3 x 80.9 mm
