OpenScan-org/OpenScan-Design/files/Midi/V2.4/STL/optional-dome-adapter (Meshed).stl

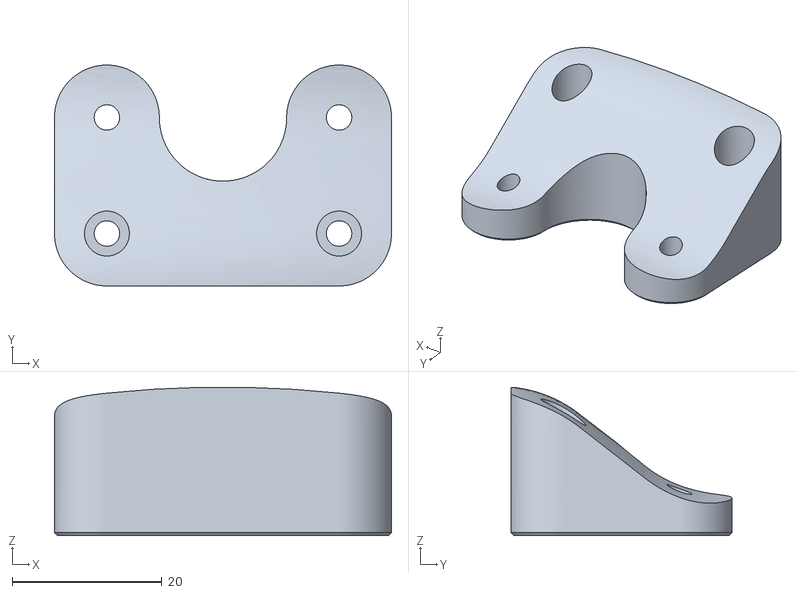
[picture p97: CAD file, 2025-03-17]
files/Midi/V2.4/STL/optional-dome-adapter (Meshed).stl
45.0 x 29.5 x 19.8
