OpenScan-org/OpenScan-Design/files/Mini/V2.4/STEP/2-rotor-unibody.step

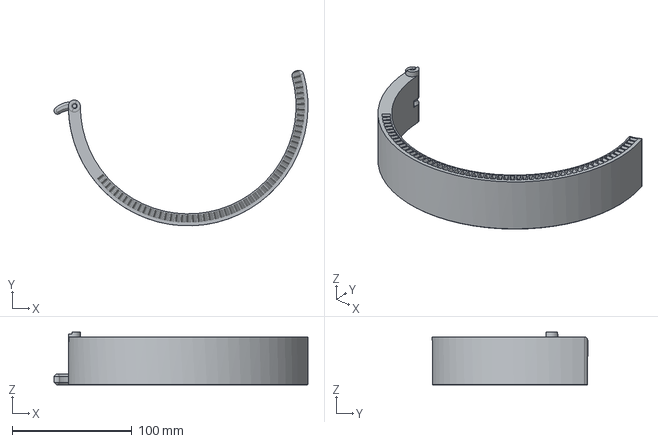
[picture p98: CAD file, 2025-06-18]
files/Mini/V2.4/STEP/2-rotor-unibody.step
212.0 x 129.8 x 44.0 mm
