OpenScan-org/OpenScan-Design/files/Classic/V1/Stand1_-_Nema17.step

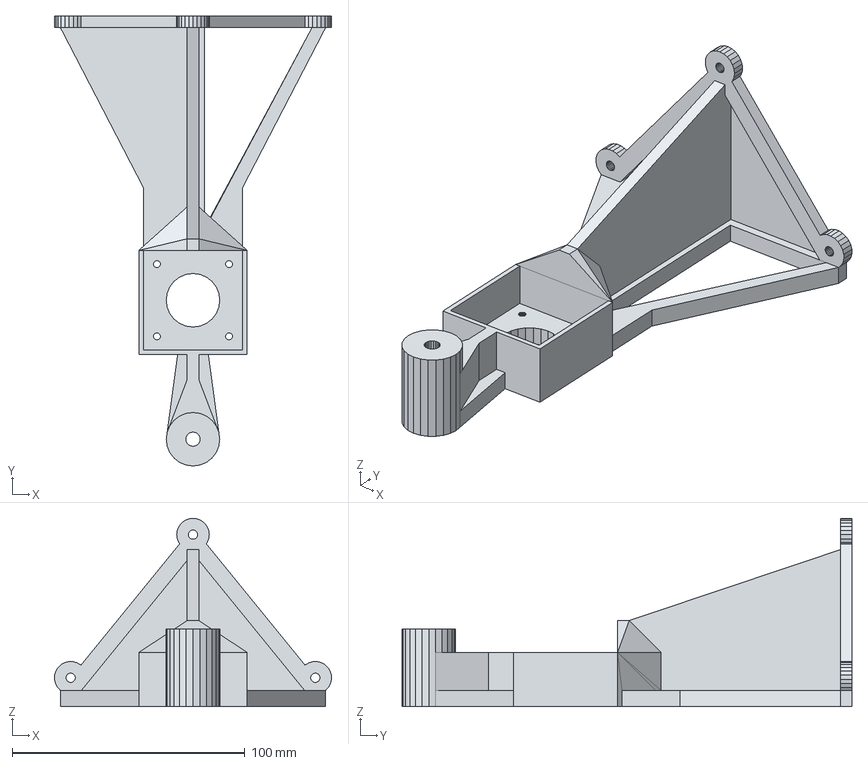
[picture p99: CAD file, 2025-07-07]
files/Classic/V1/Stand1_-_Nema17.step
119.0 x 193.3 x 80.9 mm
