OpenScan-org/OpenScan-Design/files/Imaging-Unit/STEP/6-Polarizer-Hood.step

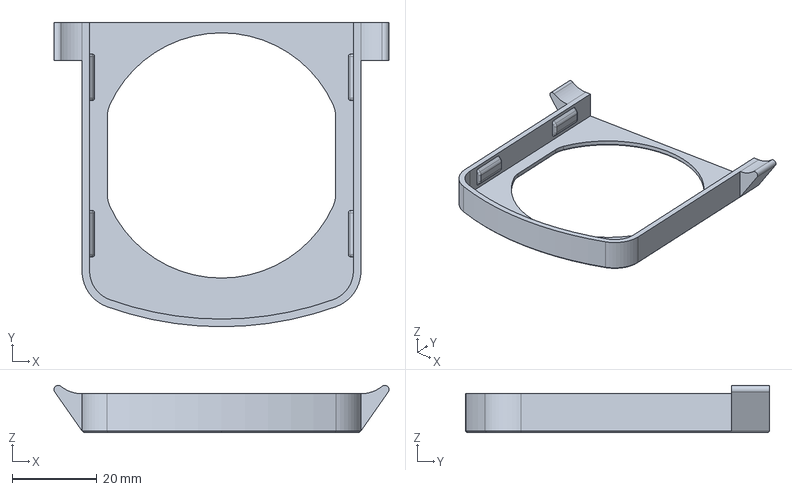
[picture p100: CAD file, 2024-12-12]
files/Imaging-Unit/STEP/6-Polarizer-Hood.step
79.2 x 72.0 x 11.2 mm
