OpenScan-org/OpenScan-Design/files/Midi/V2.4/STL/optional-cylindrical-dome (Meshed).stl

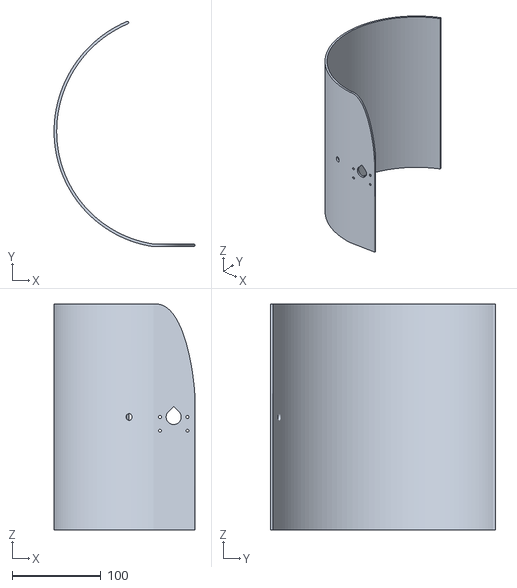
[picture p101: CAD file, 2025-03-17]
files/Midi/V2.4/STL/optional-cylindrical-dome (Meshed).stl
159.0 x 254.4 x 255.0
