OpenScan-org/OpenScan-Design/files/Classic/V1/Gear_-_Small_v2.step

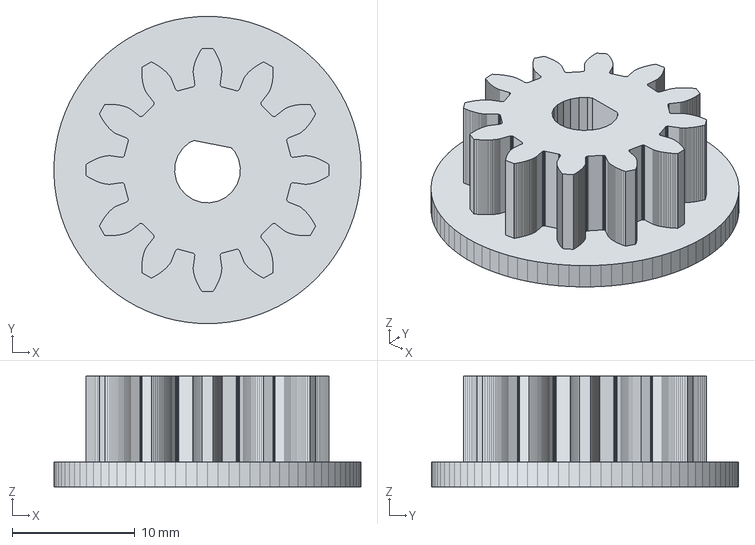
[picture p103: CAD file, 2025-07-07]
files/Classic/V1/Gear_-_Small_v2.step
25.0 x 25.0 x 9.00 mm
