OpenScan-org/OpenScan-Design/files/Midi/V2.4/STEP/3-cog-wheel-10-teeth-0.25mm.step

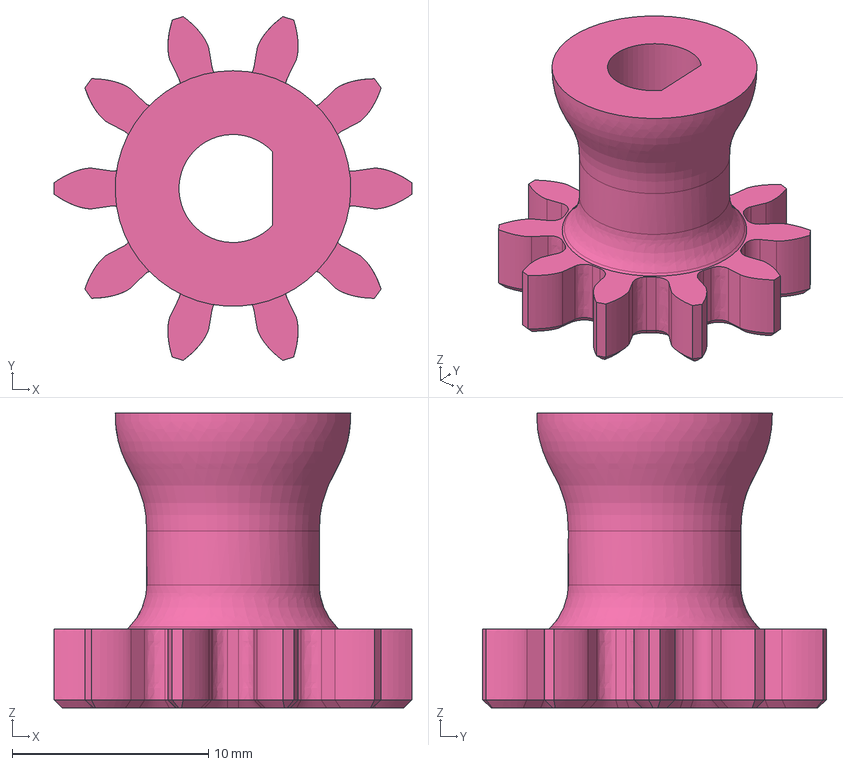
[picture p104: CAD file, 2025-03-17]
files/Midi/V2.4/STEP/3-cog-wheel-10-teeth-0.25mm.step
18.2 x 17.5 x 15.0 mm
