OpenScan-org/OpenScan-Design/files/Midi/V2.4/STL/4-electronics-cover--black-shield (Meshed).stl

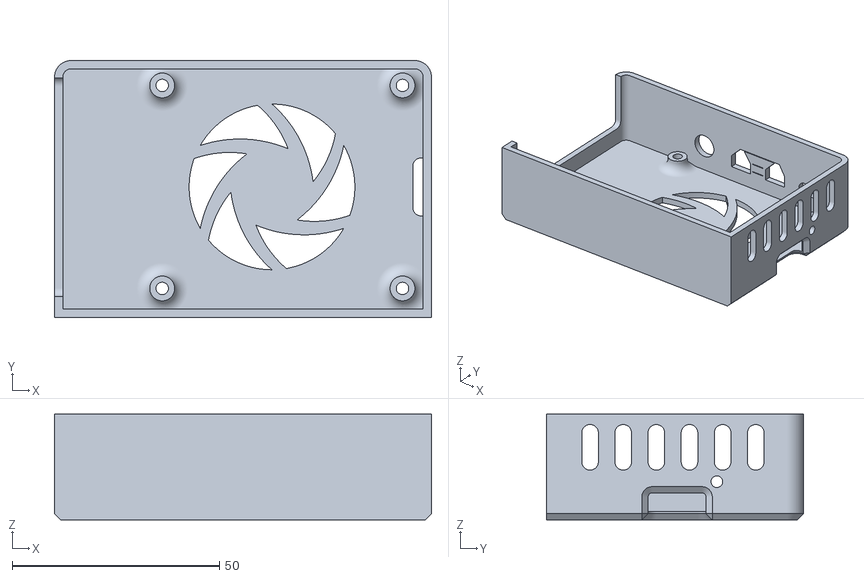
[picture p105: CAD file, 2025-03-17]
files/Midi/V2.4/STL/4-electronics-cover--black-shield (Meshed).stl
91.0 x 62.0 x 25.5
