OpenScan-org/OpenScan-Design/files/Classic/V1/Adapter1.step

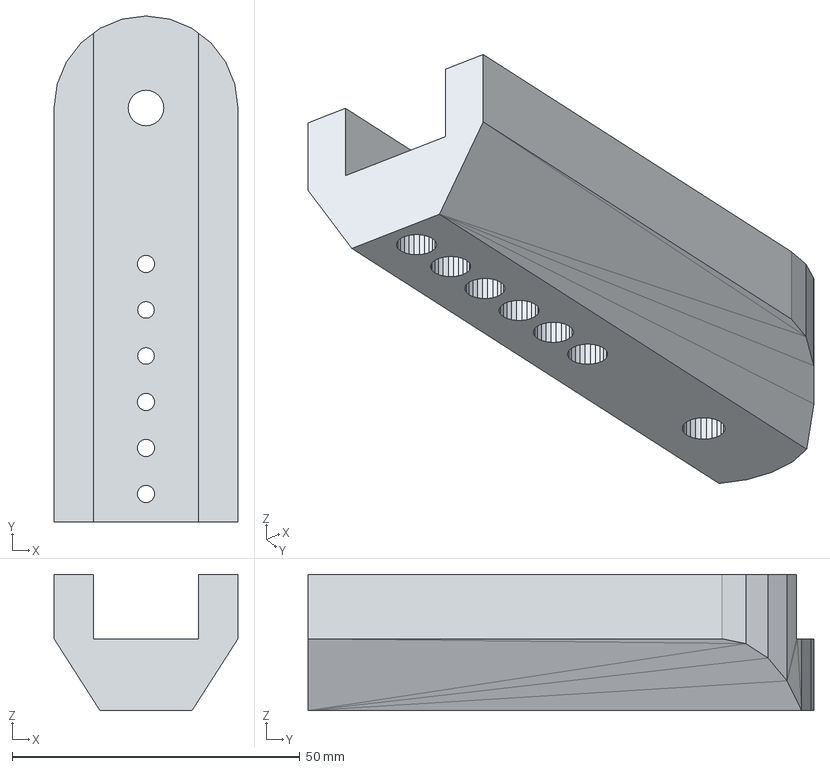
[picture p106: CAD file, 2025-07-07]
files/Classic/V1/Adapter1.step
32.0 x 88.0 x 23.7 mm
