OpenScan-org/OpenScan-Design/files/Midi/V2.4/STL/5-base-cover--green-shield (Meshed).stl

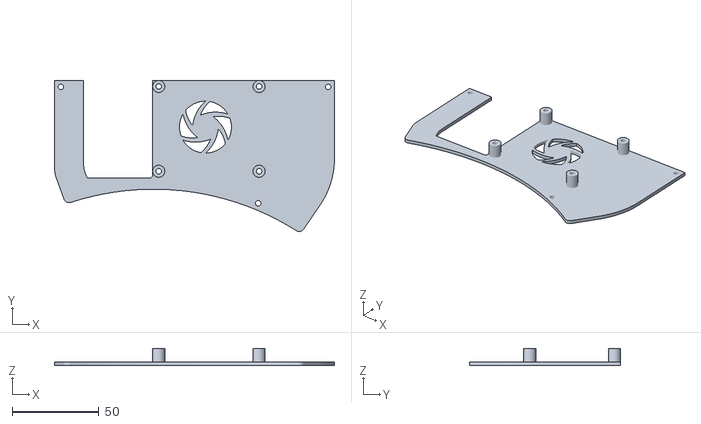
[picture p107: CAD file, 2024-12-12]
files/Midi/V2.4/STL/5-base-cover--green-shield (Meshed).stl
161.8 x 87.4 x 10.0
