OpenScan-org/OpenScan-Design/files/Mini/V2.4/STL/optional-cylindrical-dome (Meshed).stl

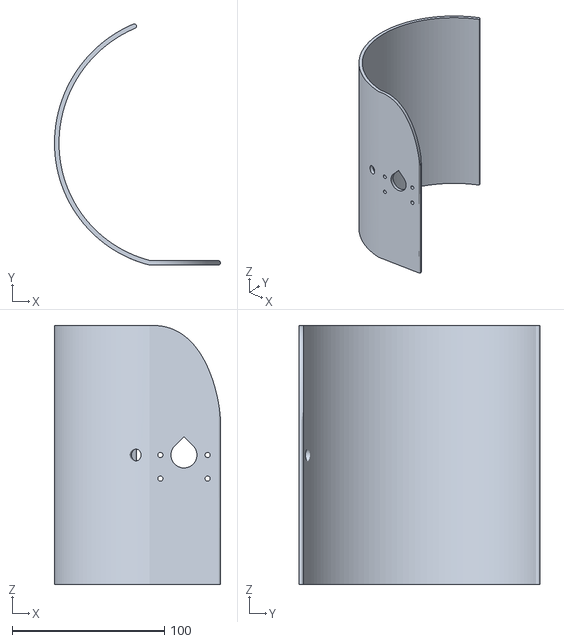
[picture p108: CAD file, 2025-03-17]
files/Mini/V2.4/STL/optional-cylindrical-dome (Meshed).stl
109.0 x 158.4 x 170.0
