OpenScan-org/OpenScan-Design/files/Classic/V1/Control_module.step

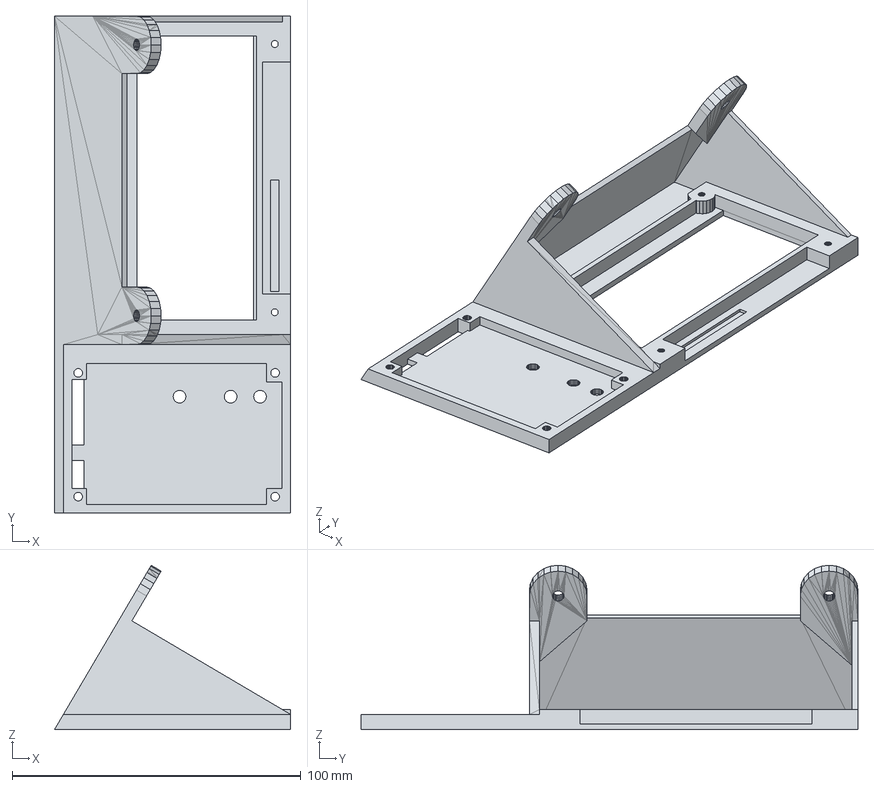
[picture p109: CAD file, 2025-07-07]
files/Classic/V1/Control_module.step
81.9 x 172.2 x 57.0 mm
