OpenScan-org/OpenScan-Design/files/Midi/V2.4/STL/4-electronics-cover-green-shield (Meshed).stl

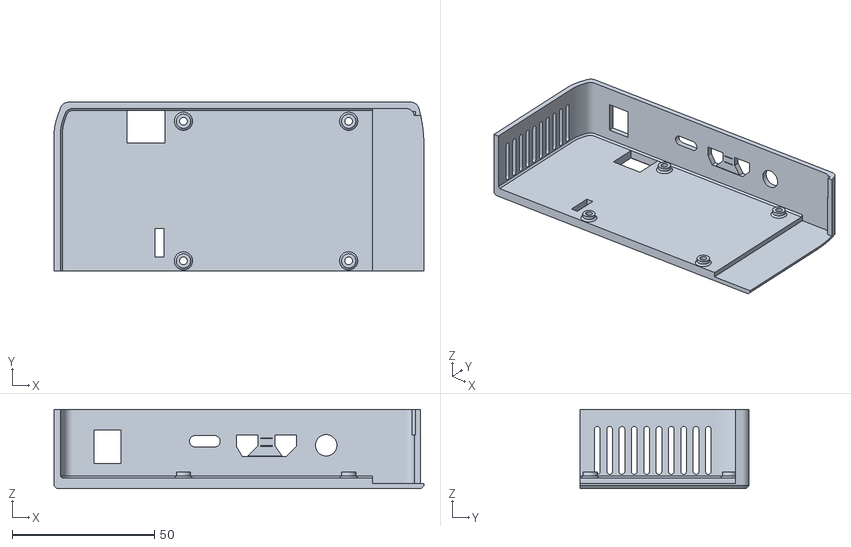
[picture p110: CAD file, 2024-12-12]
files/Midi/V2.4/STL/4-electronics-cover-green-shield (Meshed).stl
129.9 x 59.2 x 27.8
