OpenScan-org/OpenScan-Design/files/Mini/V2.4/STL/5-base-cover--green-shield (Meshed).stl

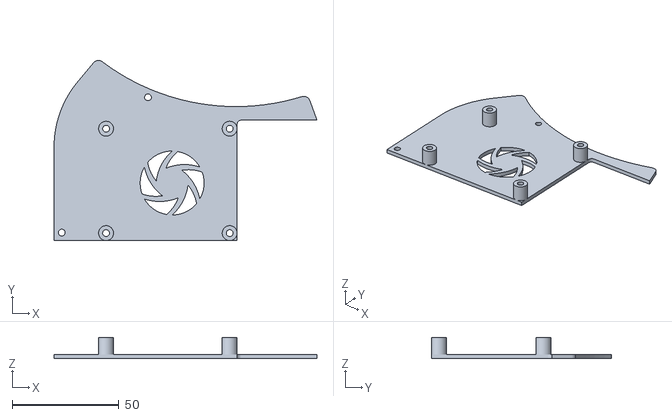
[picture p111: CAD file, 2024-12-12]
files/Mini/V2.4/STL/5-base-cover--green-shield (Meshed).stl
123.4 x 84.5 x 10.0
