OpenScan-org/OpenScan-Design/files/Classic/V1/Polarizer Classic_translucent.stl

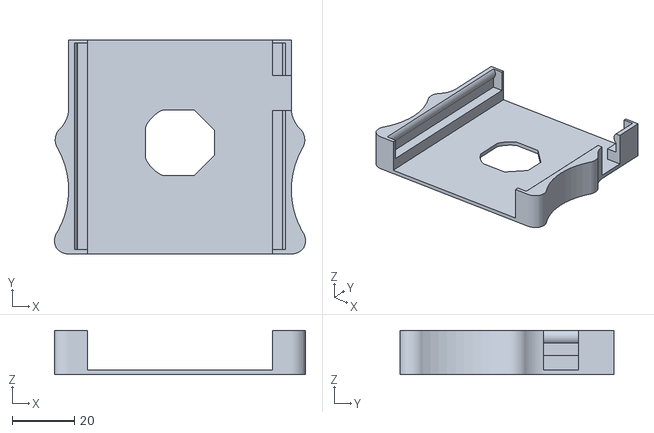
[picture p112: CAD file, 2025-02-04]
files/Classic/V1/Polarizer Classic_translucent.stl
80.9 x 69.0 x 14.2
