OpenScan-org/OpenScan-Design/files/Midi/V2.4/STEP/optional-spherical-dome.step

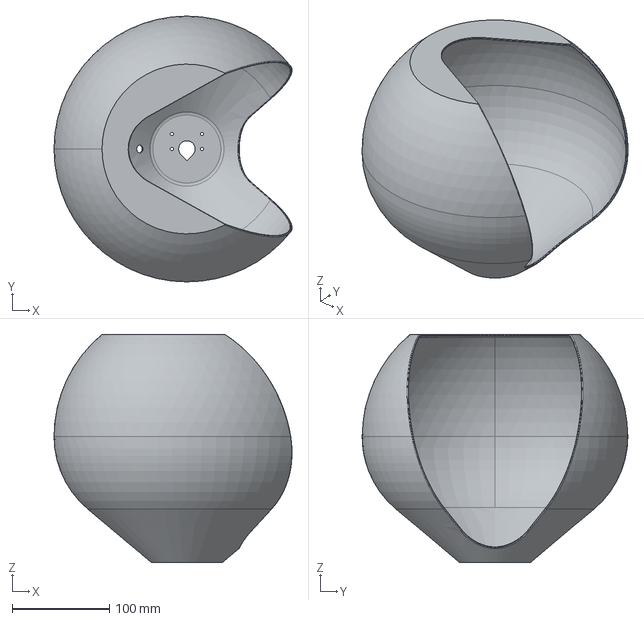
[picture p113: CAD file, 2025-03-17]
files/Midi/V2.4/STEP/optional-spherical-dome.step
245.3 x 274.0 x 235.4 mm
