OpenScan-org/OpenScan-Design/files/Mini/V2.4/STEP/optional-spherical-dome.step

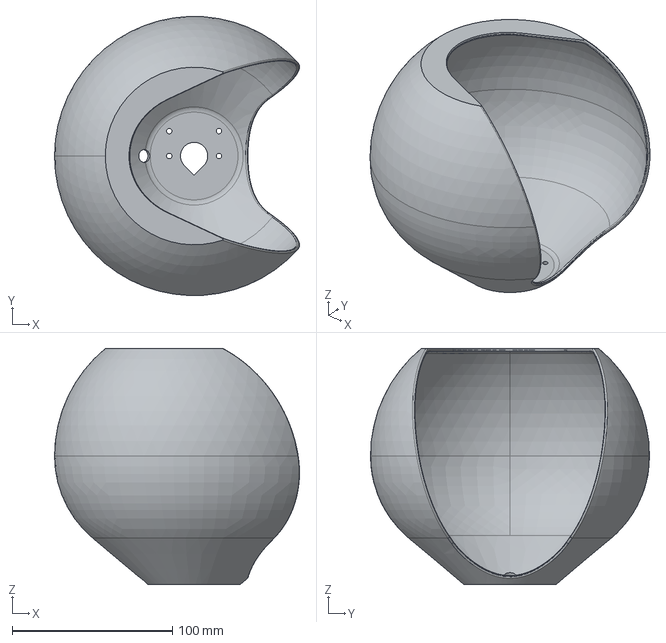
[picture p114: CAD file, 2025-03-17]
files/Mini/V2.4/STEP/optional-spherical-dome.step
152.7 x 173.9 x 147.1 mm
