OpenScan-org/OpenScan-Design/files/Midi/V2.4/STEP/optional-dome-adapter.step

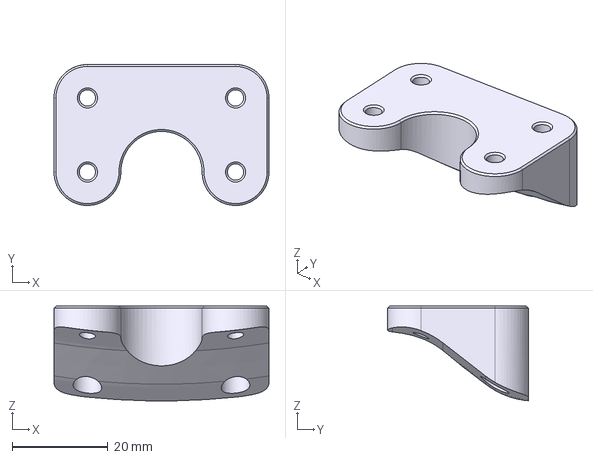
[picture p116: CAD file, 2025-03-17]
files/Midi/V2.4/STEP/optional-dome-adapter.step
45.0 x 29.5 x 19.8 mm
