OpenScan-org/OpenScan-Design/files/Classic/V1/Polarizer Classic_black_presupported.stl

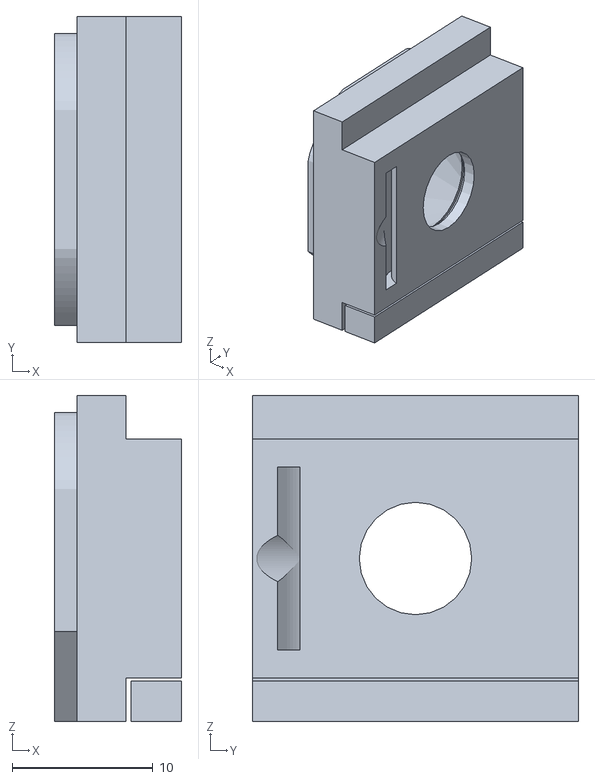
[picture p117: CAD file, 2025-02-04]
files/Classic/V1/Polarizer Classic_black_presupported.stl
9.07 x 23.2 x 23.2
