OpenScan-org/OpenScan-Design/files/Mini/V2.4/STEP/optional-dome-adapter.step

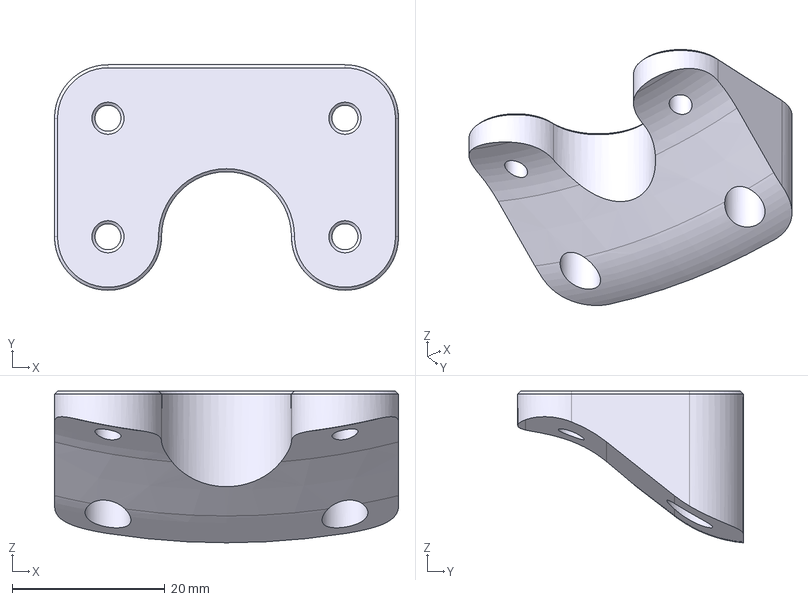
[picture p118: CAD file, 2025-03-17]
files/Mini/V2.4/STEP/optional-dome-adapter.step
45.0 x 29.5 x 19.8 mm
