OpenScan-org/OpenScan-Design/files/Classic/V1/Pi Shield_RPi_with_Ringlight_and_Network+USB.stl

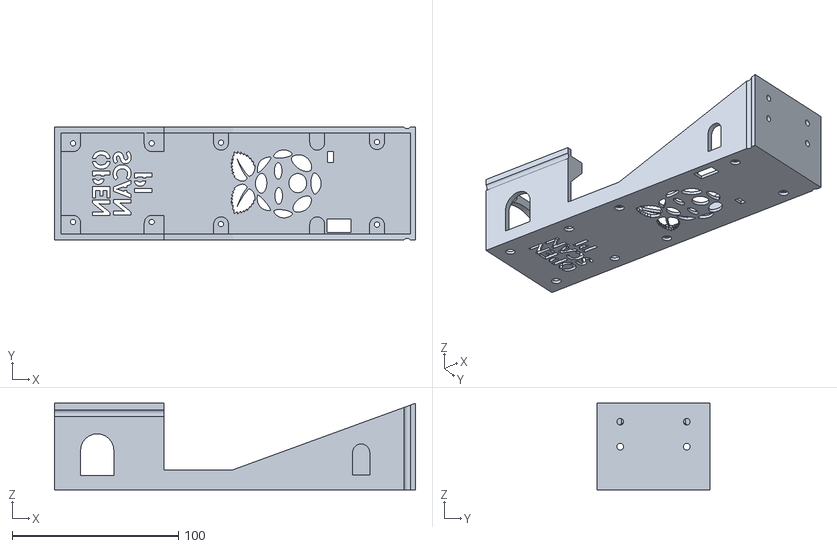
[picture p119: CAD file, 2024-02-25]
files/Classic/V1/Pi Shield_RPi_with_Ringlight_and_Network+USB.stl
217.0 x 68.0 x 52.0
