OpenScan-org/OpenScan-Design/files/Classic/V1/Adapter2_-_Gear_large.stl

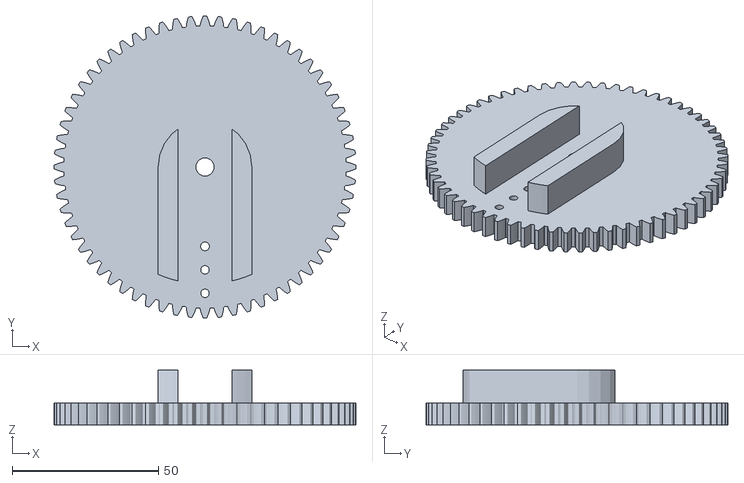
[picture p120: CAD file, 2023-03-31]
files/Classic/V1/Adapter2_-_Gear_large.stl
103.1 x 103.1 x 18.7
