OpenScan-org/OpenScan-Design/files/Classic/V1/Pi Shield_Base_Slider.stl

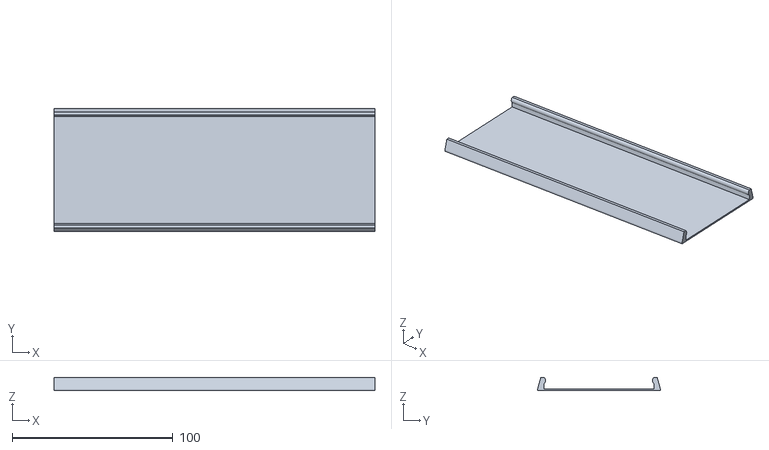
[picture p121: CAD file, 2023-03-31]
files/Classic/V1/Pi Shield_Base_Slider.stl
200.0 x 76.5 x 8.35
