OpenScan-org/OpenScan-Design/files/Classic/V1/Pi Shield_RPi_without_Ringlight.stl

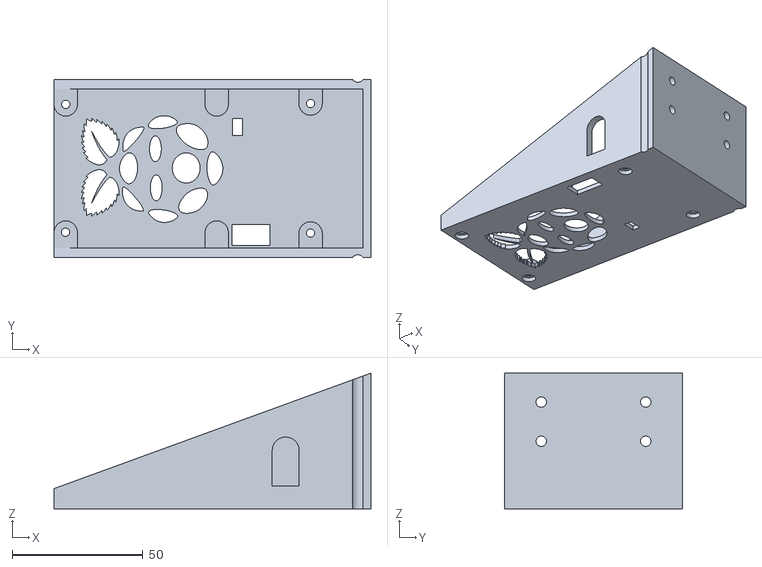
[picture p122: CAD file, 2023-03-31]
files/Classic/V1/Pi Shield_RPi_without_Ringlight.stl
121.4 x 68.0 x 52.0
