OpenScan-org/OpenScan-Design/images/assembly/04_base_optional2.JPG

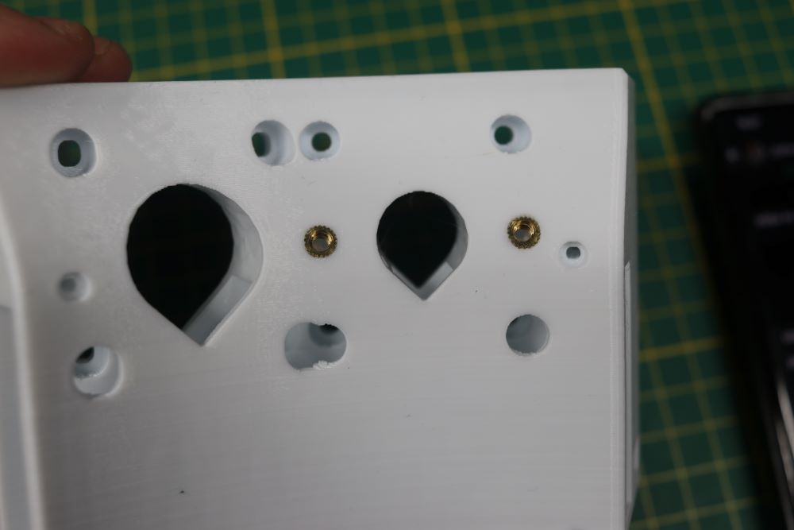
images/assembly/04_base_optional2.JPG
