OpenScan-org/OpenScan-Design/images/assembly/05.0_base_endstop.JPG

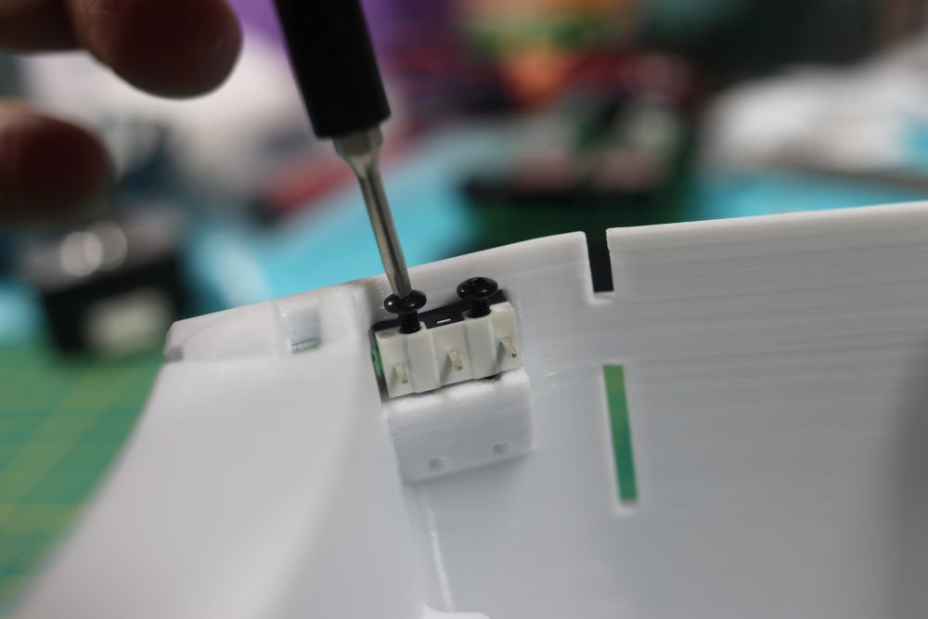
images/assembly/05.0_base_endstop.JPG
