OpenScan-org/OpenScan-Design/images/assembly/05.2_endstop_triggered.JPG

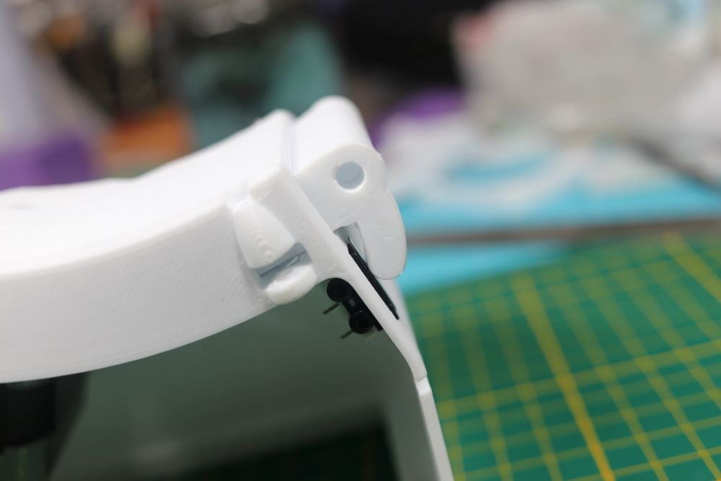
images/assembly/05.2_endstop_triggered.JPG
