OpenScan-org/OpenScan-Design/images/assembly/06_base_motor.JPG

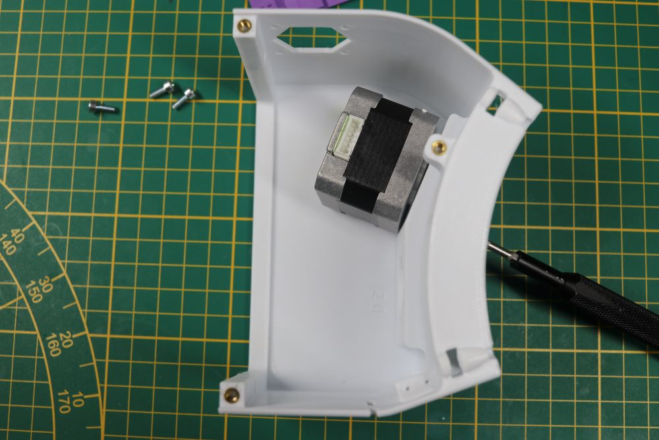
images/assembly/06_base_motor.JPG
