OpenScan-org/OpenScan-Design/images/assembly/09.0_elec_cover_green-shield.JPG

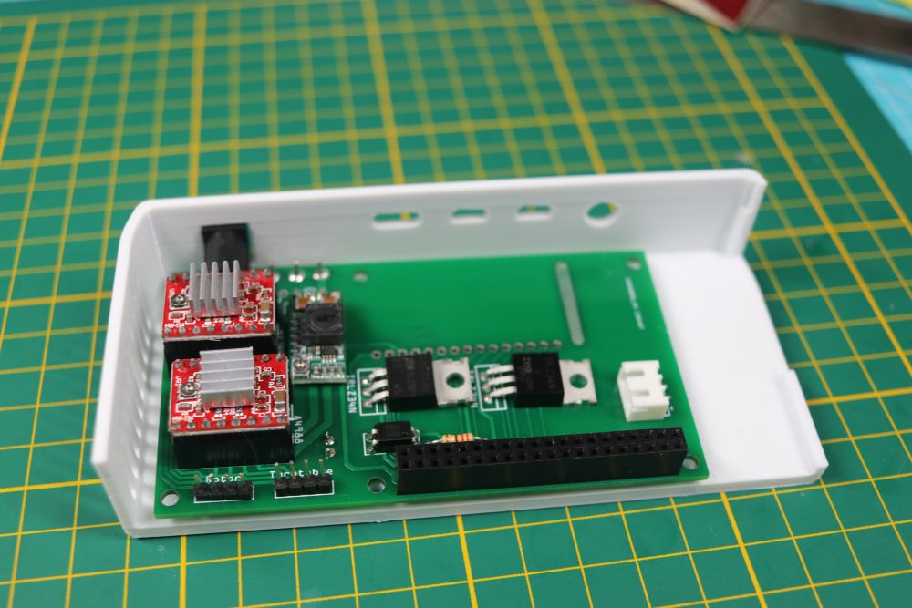
images/assembly/09.0_elec_cover_green-shield.JPG
