OpenScan-org/OpenScan-Design/images/assembly/11.0_CSI_orientation_RPi.JPG

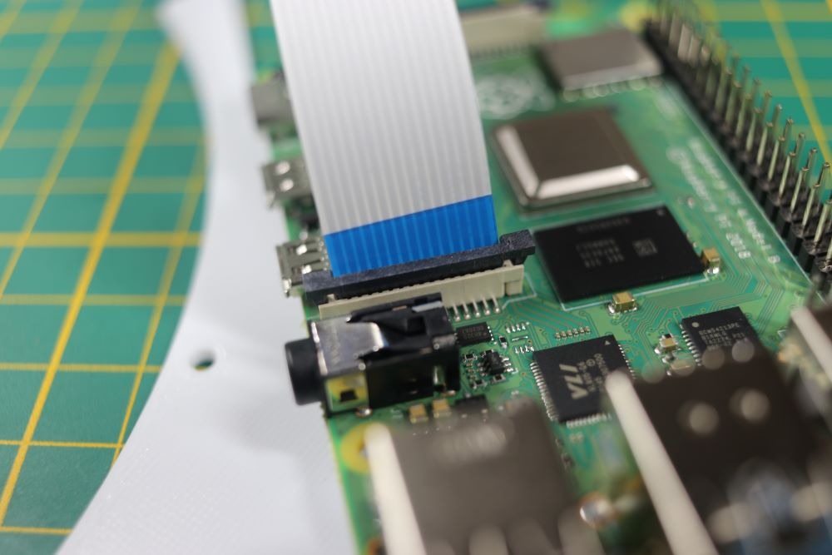
images/assembly/11.0_CSI_orientation_RPi.JPG
