OpenScan-org/OpenScan-Design/images/assembly/17.0_rotor_m3x40.JPG

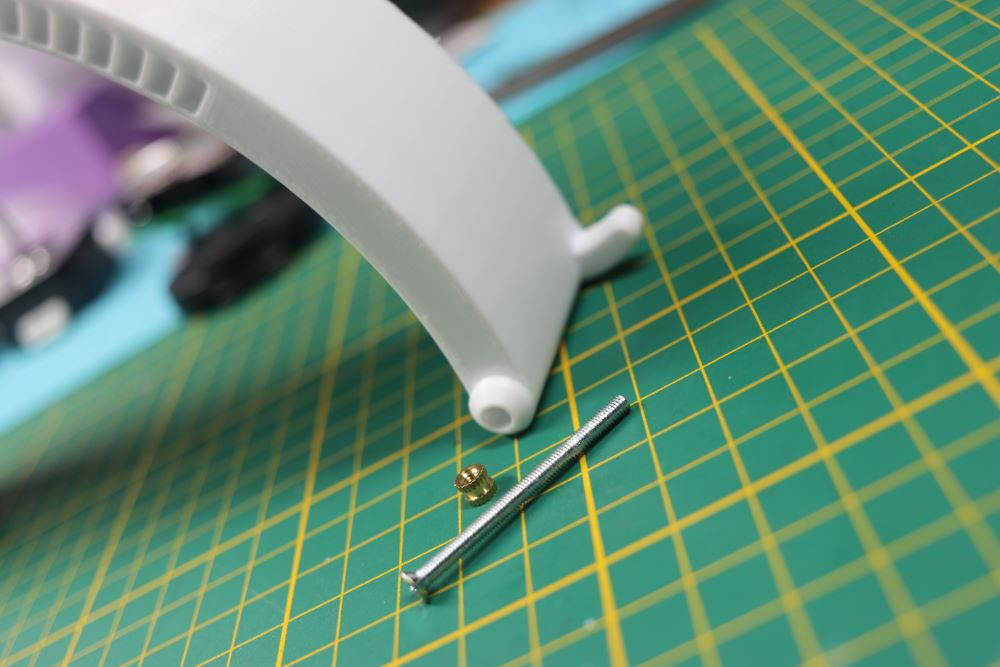
images/assembly/17.0_rotor_m3x40.JPG
