OpenScan-org/OpenScan-Design/images/assembly/17.1_rotor_assembly.jpg

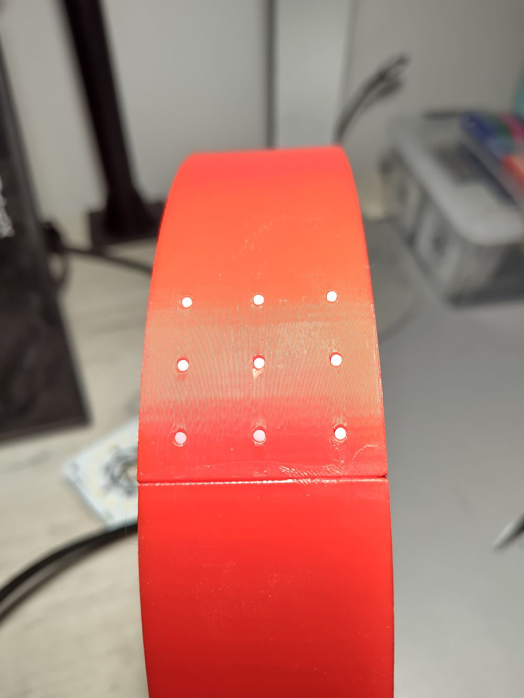
images/assembly/17.1_rotor_assembly.jpg
