OpenScan-org/OpenScan-Design/images/assembly/18.0_IU-cover_inserts.JPG

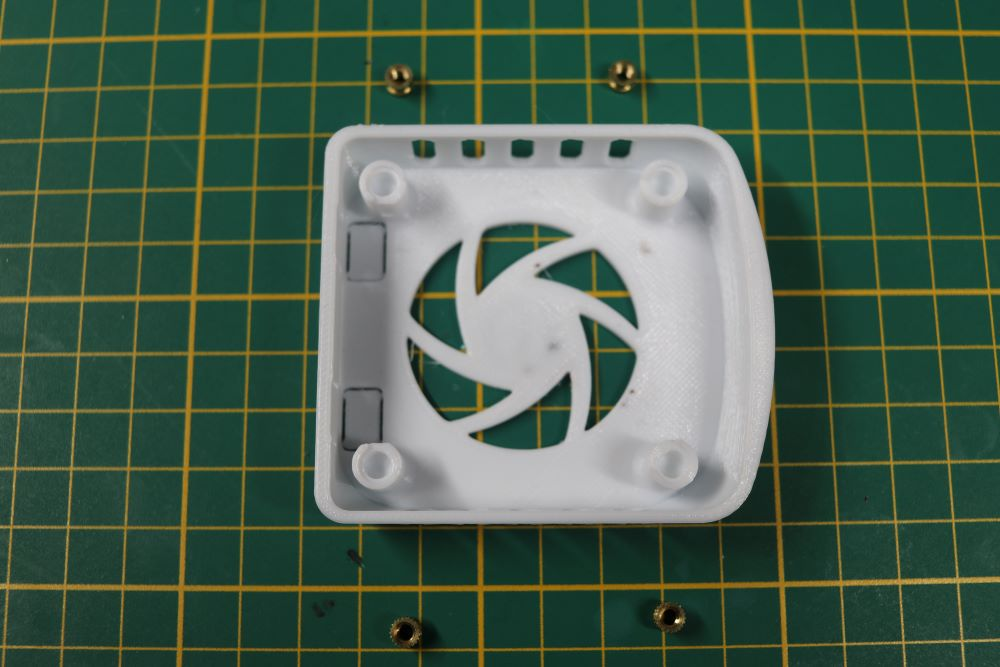
images/assembly/18.0_IU-cover_inserts.JPG
