OpenScan-org/OpenScan-Design/images/assembly/26_OpenScan_assembled.JPG

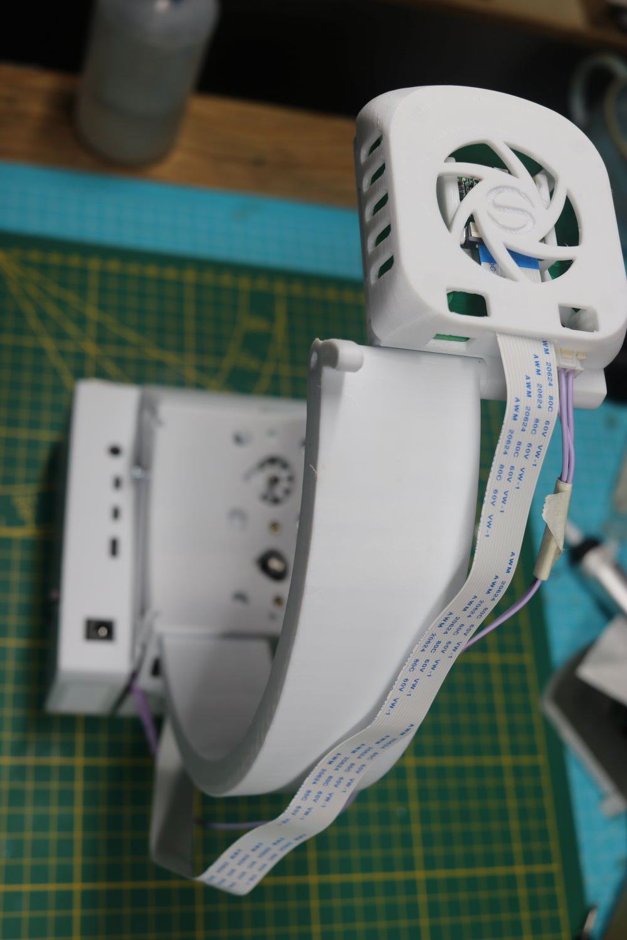
images/assembly/26_OpenScan_assembled.JPG
